DillonSimeone/ConfluenceTactoLuminateBracelet/images/datagloves/5DTDataGlove5Ultra.webp

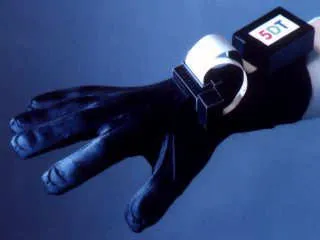
images/datagloves/5DTDataGlove5Ultra.webp
