DillonSimeone/ConfluenceTactoLuminateBracelet/images/datagloves/10FingerFlexGloves.webp

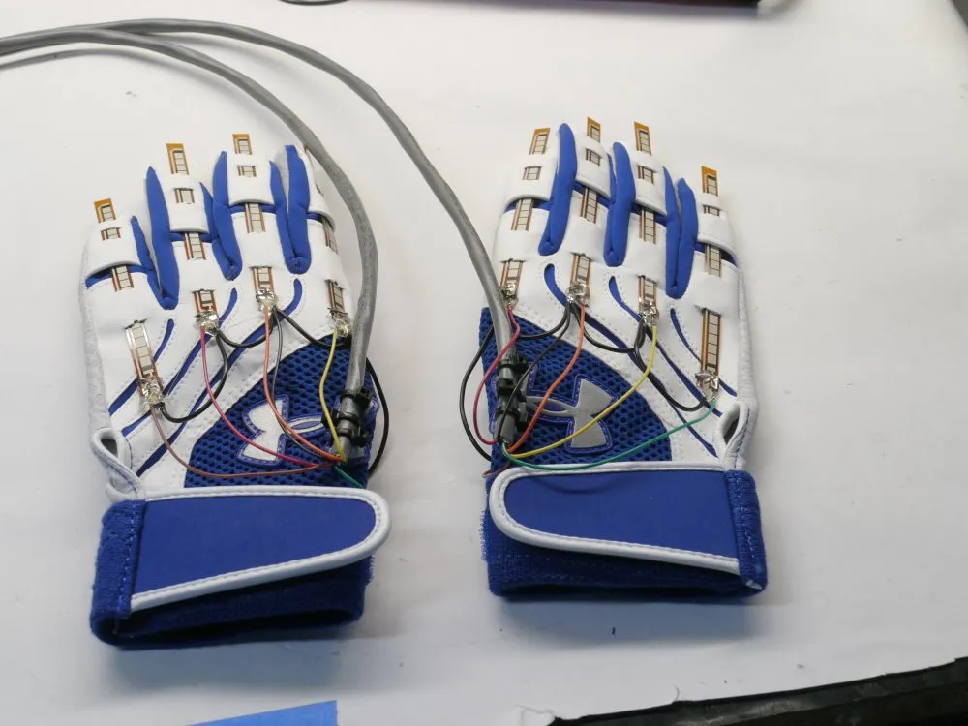
images/datagloves/10FingerFlexGloves.webp
