DillonSimeone/ConfluenceTactoLuminateBracelet/images/datagloves/acceleglove.webp

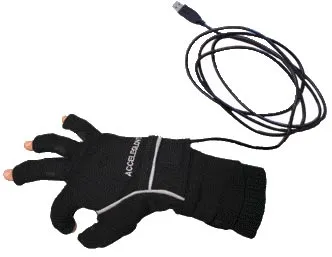
images/datagloves/acceleglove.webp
