DillonSimeone/ConfluenceTactoLuminateBracelet/images/datagloves/aura.webp

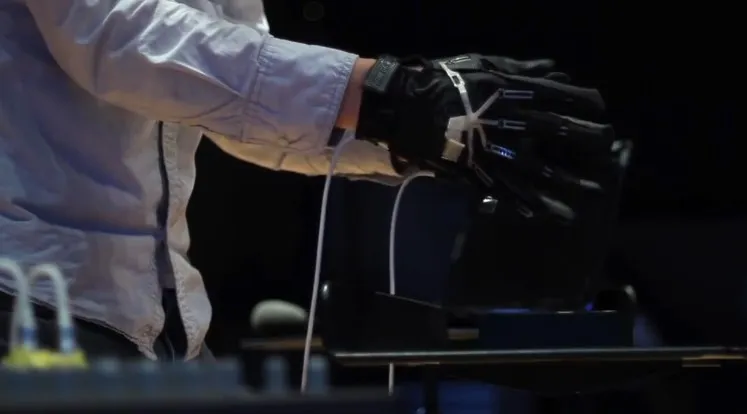
images/datagloves/aura.webp
