DillonSimeone/ConfluenceTactoLuminateBracelet/images/datagloves/CrochetGloves.webp

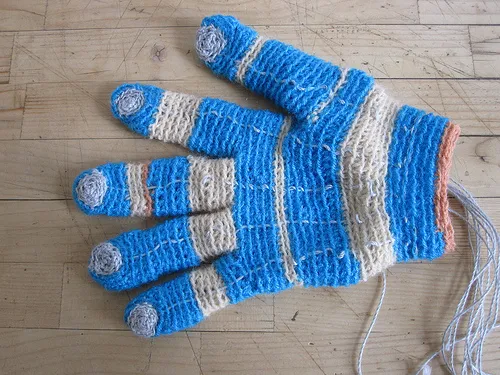
images/datagloves/CrochetGloves.webp
