DillonSimeone/ConfluenceTactoLuminateBracelet/images/datagloves/Cybergloves.webp

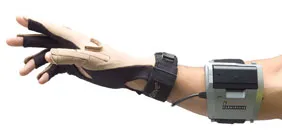
images/datagloves/Cybergloves.webp
