DillonSimeone/ConfluenceTactoLuminateBracelet/images/datagloves/Data_Glove_System.webp

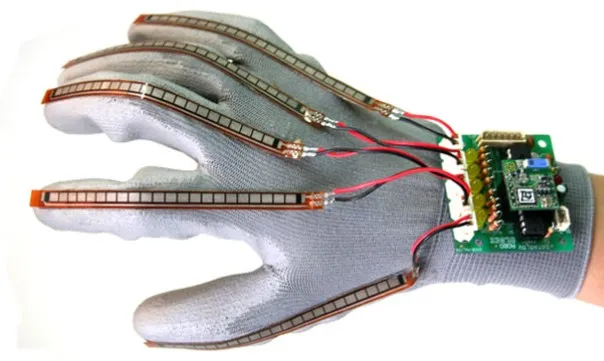
images/datagloves/Data_Glove_System.webp
