DillonSimeone/ConfluenceTactoLuminateBracelet/images/datagloves/DataGloveDarmstadt.webp

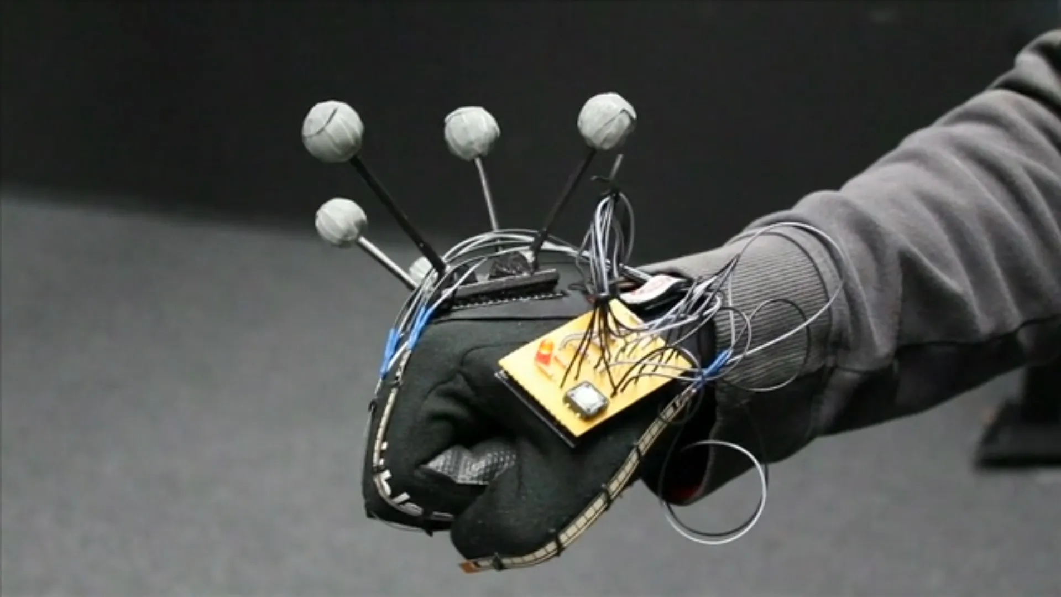
images/datagloves/DataGloveDarmstadt.webp
