DillonSimeone/ConfluenceTactoLuminateBracelet/images/datagloves/Digits.webp

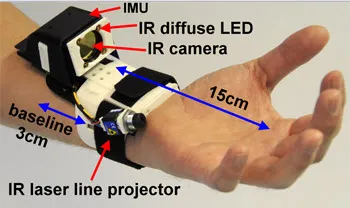
images/datagloves/Digits.webp
