DillonSimeone/ConfluenceTactoLuminateBracelet/images/datagloves/DjGLove.webp

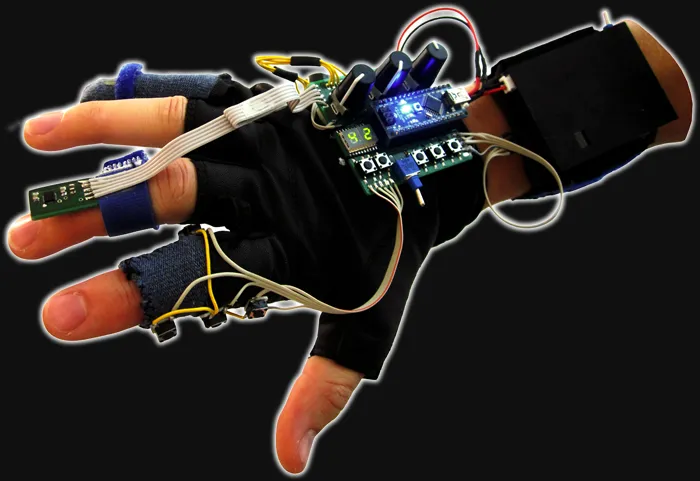
images/datagloves/DjGLove.webp
