DillonSimeone/ConfluenceTactoLuminateBracelet/images/datagloves/drawdioGlove.webp

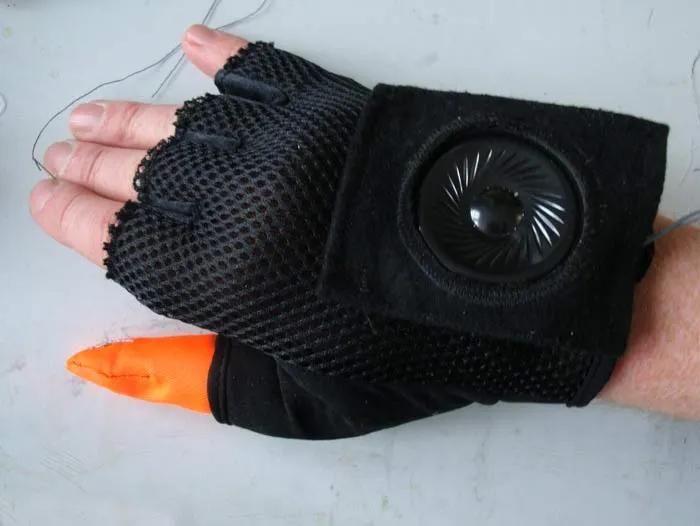
images/datagloves/drawdioGlove.webp
