DillonSimeone/ConfluenceTactoLuminateBracelet/images/datagloves/Exolux.webp

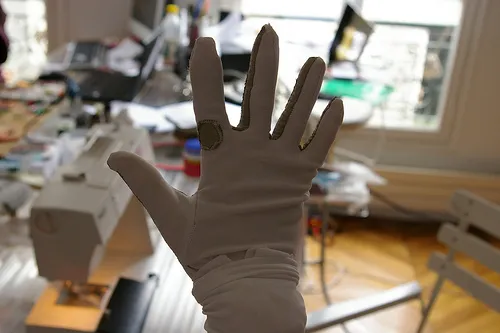
images/datagloves/Exolux.webp
