DillonSimeone/ConfluenceTactoLuminateBracelet/images/datagloves/EXOSDexterousHandMaster.webp

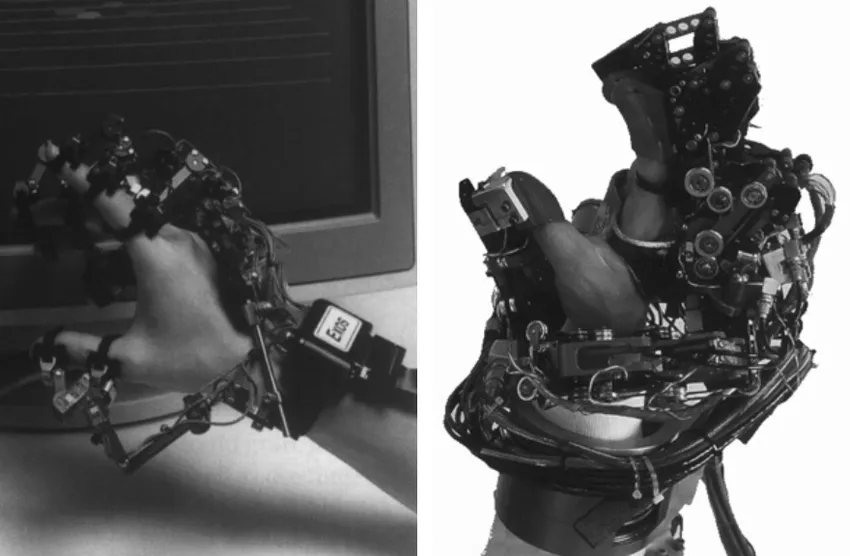
images/datagloves/EXOSDexterousHandMaster.webp
