DillonSimeone/ConfluenceTactoLuminateBracelet/images/datagloves/fingerPiano.webp

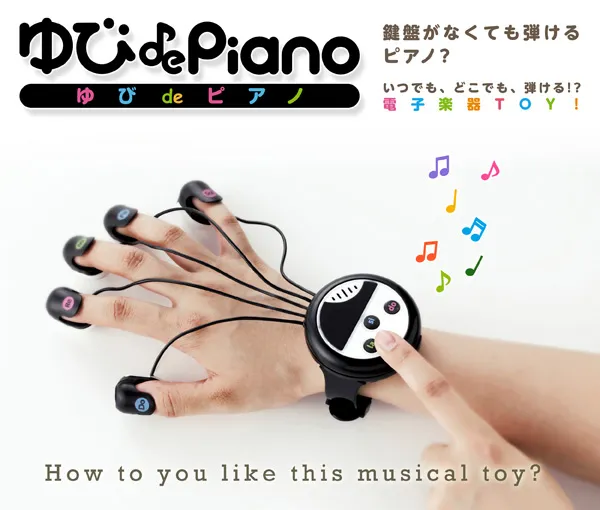
images/datagloves/fingerPiano.webp
