DillonSimeone/ConfluenceTactoLuminateBracelet/images/datagloves/FingerTPSII.webp

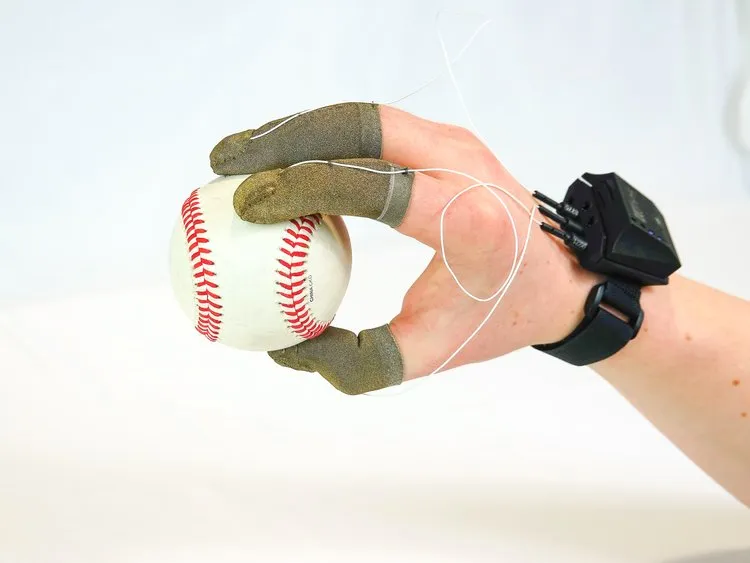
images/datagloves/FingerTPSII.webp
