DillonSimeone/ConfluenceTactoLuminateBracelet/images/datagloves/FranziskaBaumannSensorgloves.webp

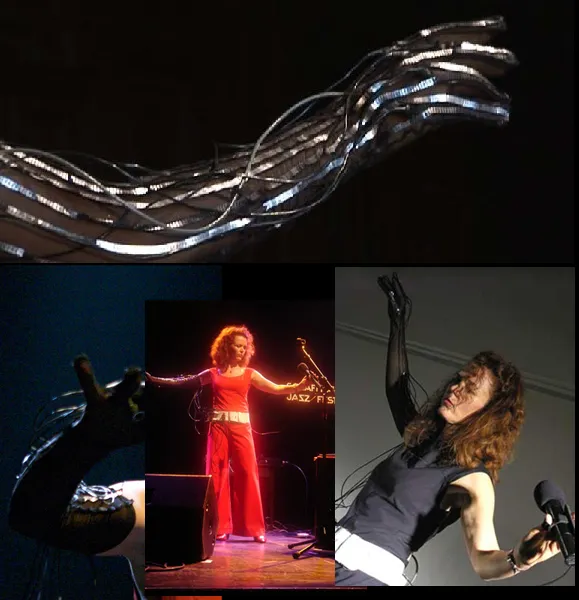
images/datagloves/FranziskaBaumannSensorgloves.webp
