DillonSimeone/ConfluenceTactoLuminateBracelet/images/datagloves/GloveOne.webp

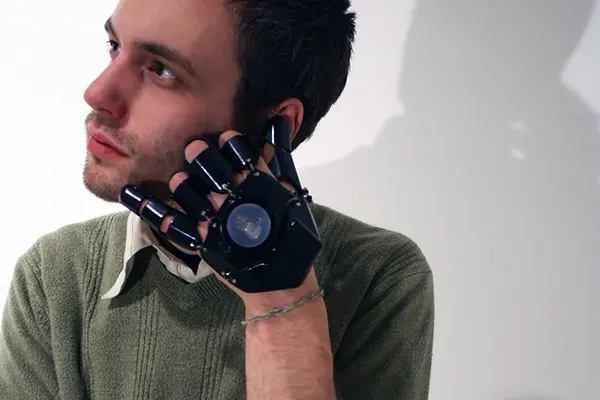
images/datagloves/GloveOne.webp
