DillonSimeone/ConfluenceTactoLuminateBracelet/images/datagloves/GlovePressureMappingSystem.webp

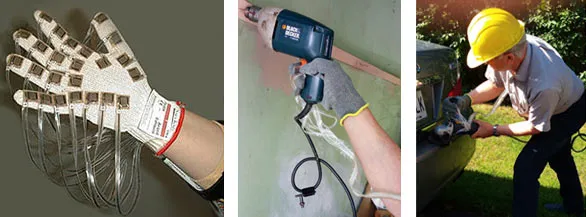
images/datagloves/GlovePressureMappingSystem.webp
