DillonSimeone/ConfluenceTactoLuminateBracelet/images/datagloves/GolanLevinHAND.webp

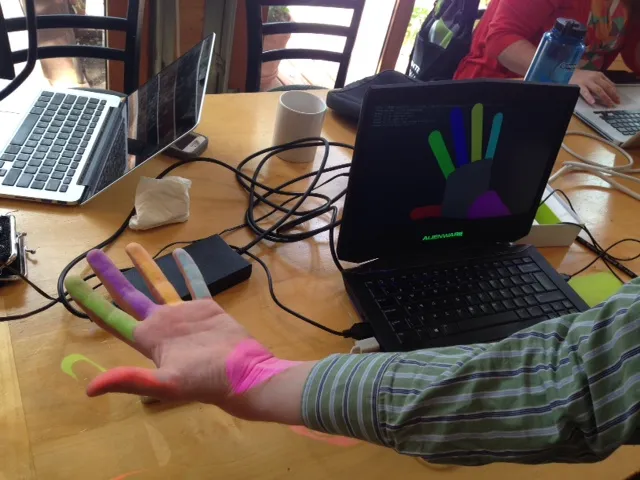
images/datagloves/GolanLevinHAND.webp
