DillonSimeone/ConfluenceTactoLuminateBracelet/images/datagloves/gStalt.webp

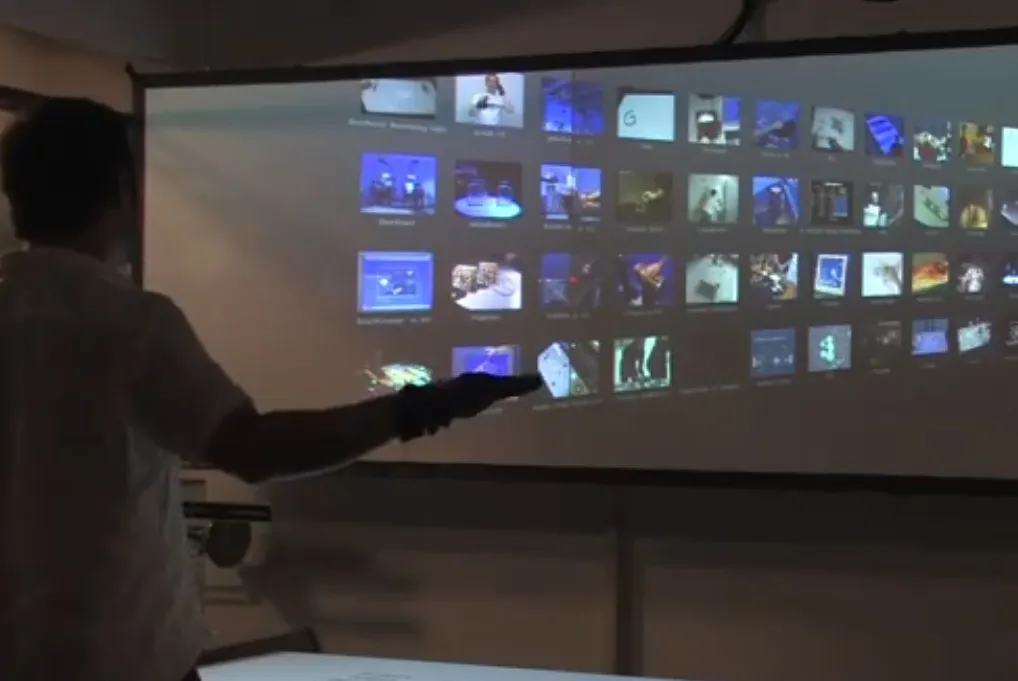
images/datagloves/gStalt.webp
