DillonSimeone/ConfluenceTactoLuminateBracelet/images/datagloves/KeyGlove.webp

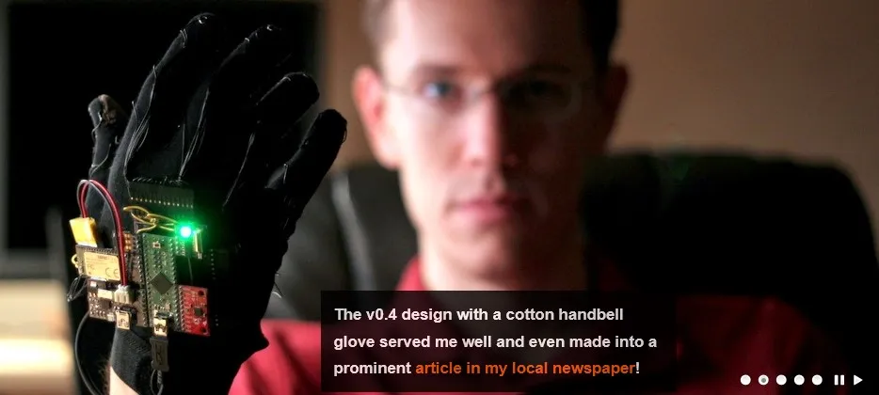
images/datagloves/KeyGlove.webp
