DillonSimeone/ConfluenceTactoLuminateBracelet/images/datagloves/ladysglove.webp

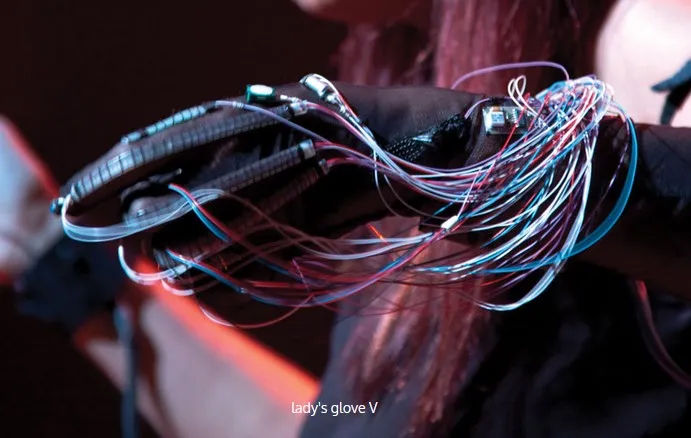
images/datagloves/ladysglove.webp
