DillonSimeone/ConfluenceTactoLuminateBracelet/images/datagloves/LuluWhite.webp

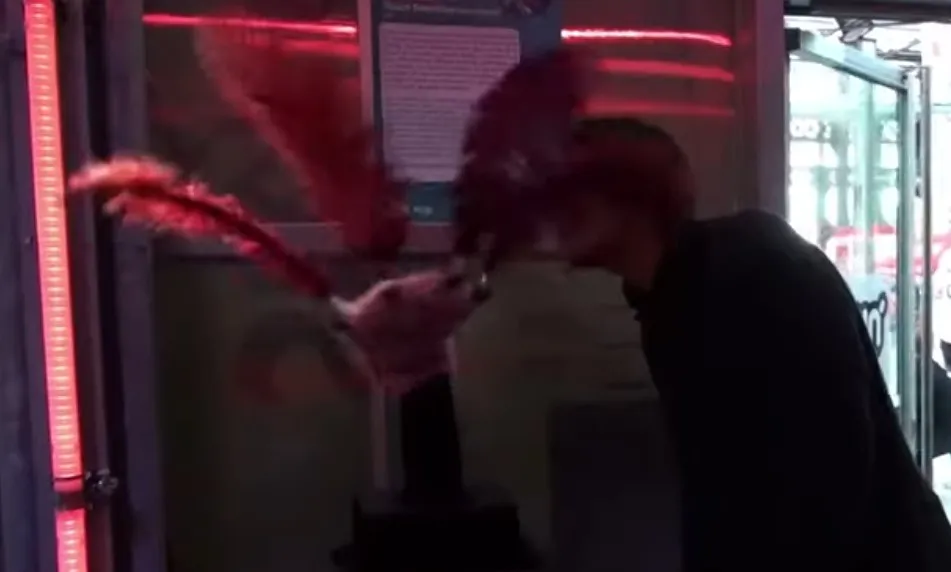
images/datagloves/LuluWhite.webp
