DillonSimeone/ConfluenceTactoLuminateBracelet/images/datagloves/Marchingbandgloves.webp

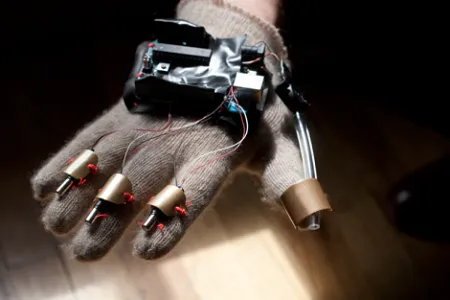
images/datagloves/Marchingbandgloves.webp
