DillonSimeone/ConfluenceTactoLuminateBracelet/images/datagloves/MediTouch-Hand-Tutor-2.webp

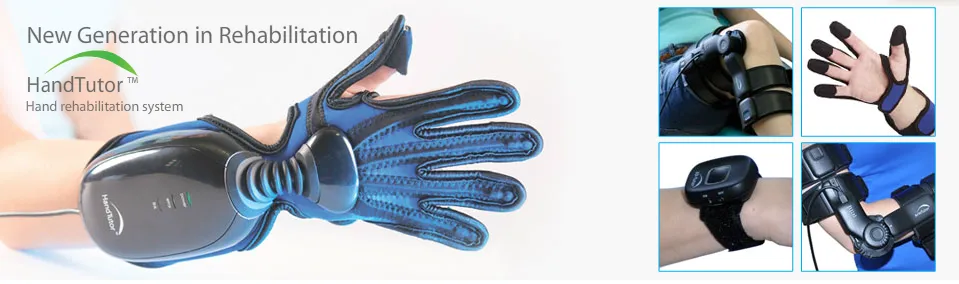
images/datagloves/MediTouch-Hand-Tutor-2.webp
