DillonSimeone/ConfluenceTactoLuminateBracelet/images/datagloves/mobile-lorm-glove-03.webp

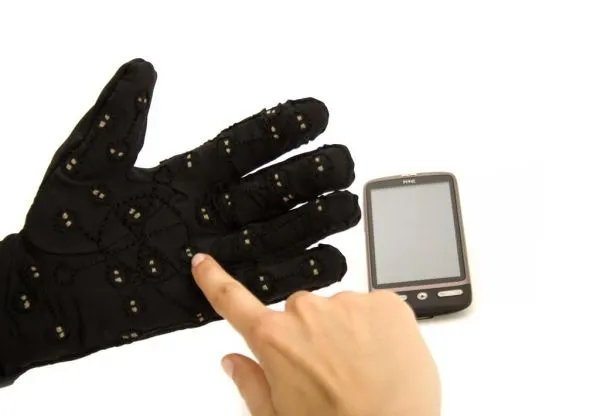
images/datagloves/mobile-lorm-glove-03.webp
