DillonSimeone/ConfluenceTactoLuminateBracelet/images/datagloves/MusicGloves.webp

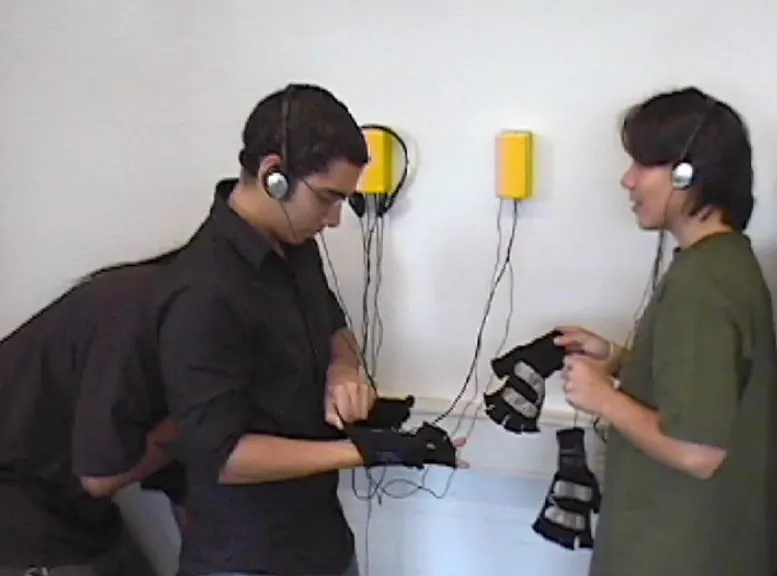
images/datagloves/MusicGloves.webp
