DillonSimeone/ConfluenceTactoLuminateBracelet/images/datagloves/peregrineglove.webp

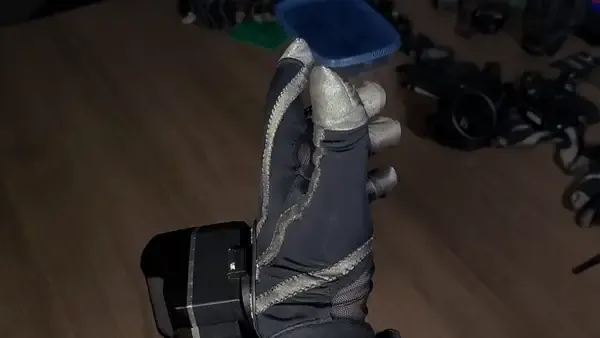
images/datagloves/peregrineglove.webp
