DillonSimeone/ConfluenceTactoLuminateBracelet/images/datagloves/PersonalInstrument.webp

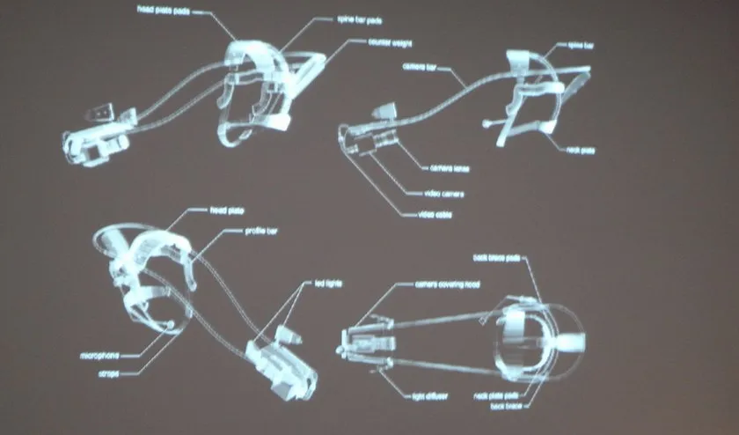
images/datagloves/PersonalInstrument.webp
