DillonSimeone/ConfluenceTactoLuminateBracelet/images/datagloves/PhaseSpaceMotionCaptureGloves.webp

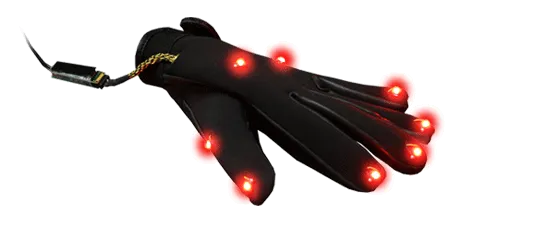
images/datagloves/PhaseSpaceMotionCaptureGloves.webp
