DillonSimeone/ConfluenceTactoLuminateBracelet/images/datagloves/PianoGloves.webp

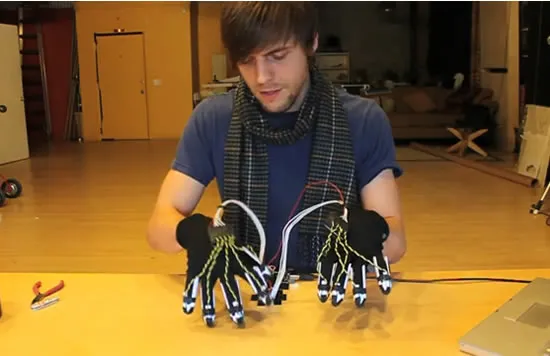
images/datagloves/PianoGloves.webp
