DillonSimeone/ConfluenceTactoLuminateBracelet/images/datagloves/pinch.webp-srcw.webp

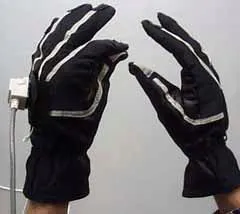
images/datagloves/pinch.webp-srcw.webp
