DillonSimeone/ConfluenceTactoLuminateBracelet/images/datagloves/plianceGloveSensor.webp

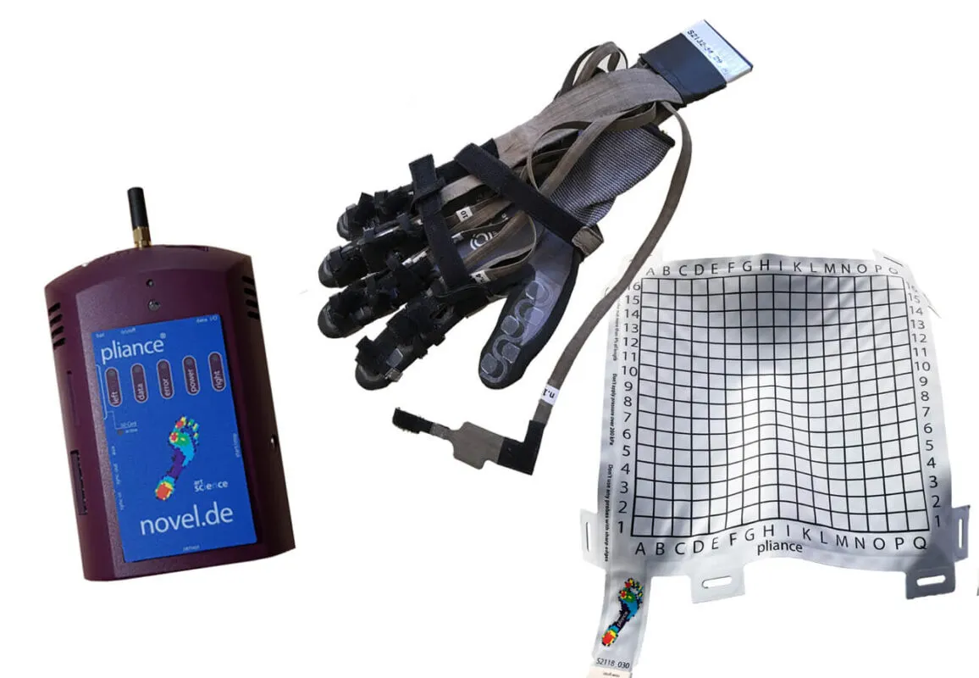
images/datagloves/plianceGloveSensor.webp
