DillonSimeone/ConfluenceTactoLuminateBracelet/images/datagloves/powerGlove.webp

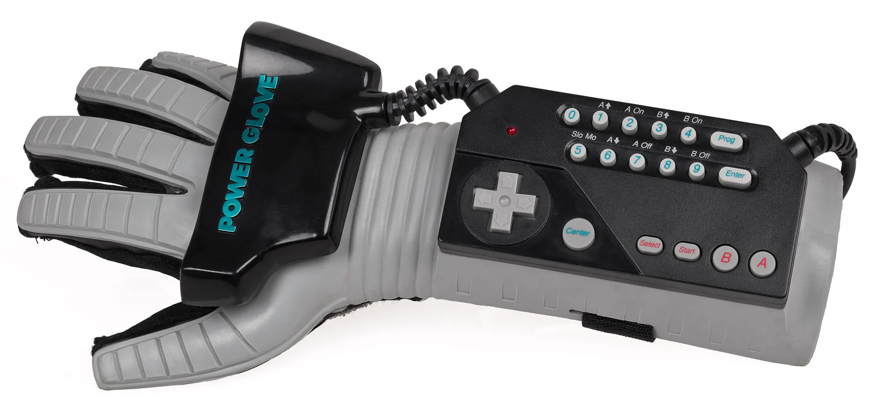
images/datagloves/powerGlove.webp
