DillonSimeone/ConfluenceTactoLuminateBracelet/images/datagloves/ProGlove.webp

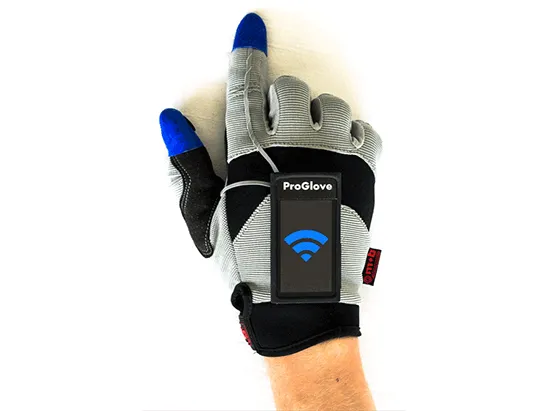
images/datagloves/ProGlove.webp
