DillonSimeone/ConfluenceTactoLuminateBracelet/images/datagloves/propinquity.webp

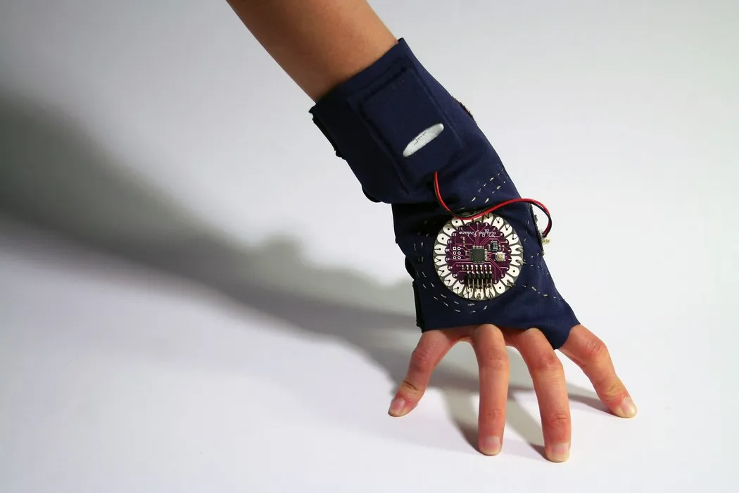
images/datagloves/propinquity.webp
