DillonSimeone/ConfluenceTactoLuminateBracelet/images/datagloves/RachelYalisoveConversationalGloves.webp

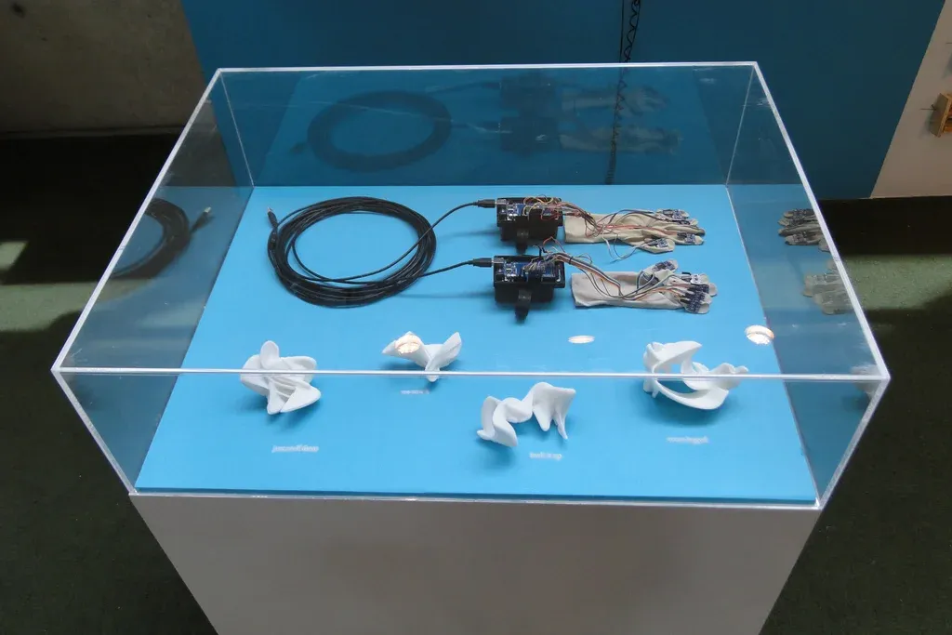
images/datagloves/RachelYalisoveConversationalGloves.webp
