DillonSimeone/ConfluenceTactoLuminateBracelet/images/datagloves/secret_keeper_72.webp

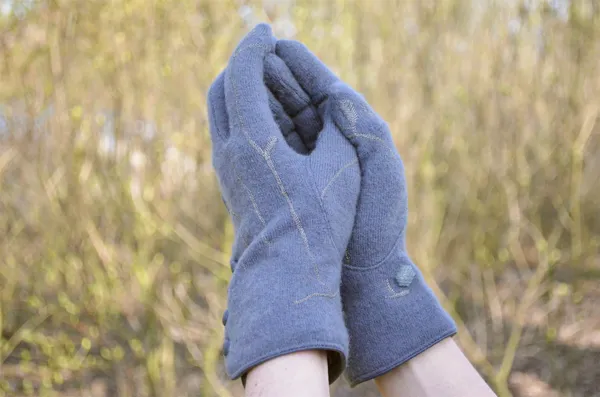
images/datagloves/secret_keeper_72.webp
