DillonSimeone/ConfluenceTactoLuminateBracelet/images/datagloves/SensitiveFingertips.webp

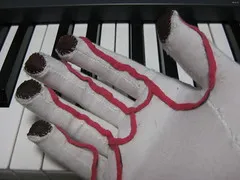
images/datagloves/SensitiveFingertips.webp
