DillonSimeone/ConfluenceTactoLuminateBracelet/images/datagloves/shakeonit.webp

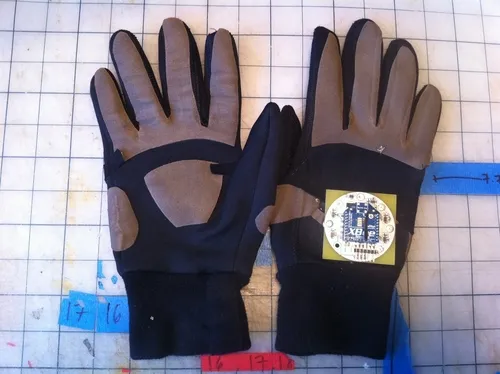
images/datagloves/shakeonit.webp
