DillonSimeone/ConfluenceTactoLuminateBracelet/images/datagloves/Signlanguagetranslation.webp

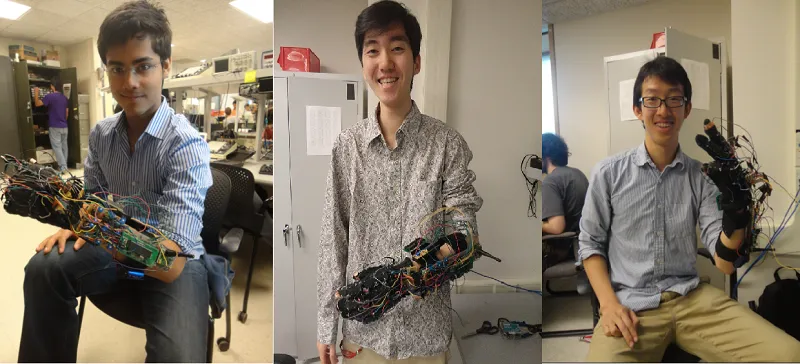
images/datagloves/Signlanguagetranslation.webp
