DillonSimeone/ConfluenceTactoLuminateBracelet/images/datagloves/sneakyGestures.webp

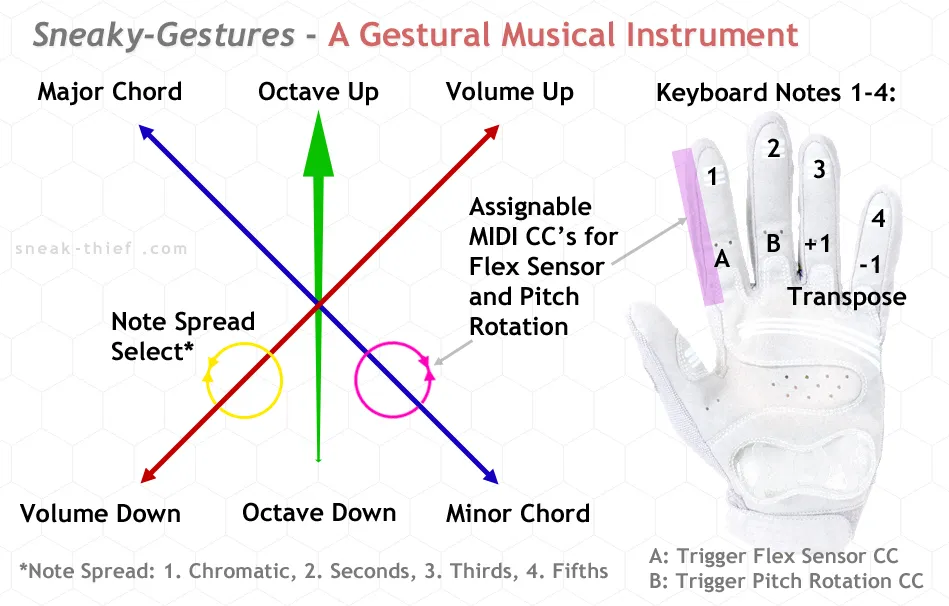
images/datagloves/sneakyGestures.webp
