DillonSimeone/ConfluenceTactoLuminateBracelet/images/datagloves/stretchSense.webp

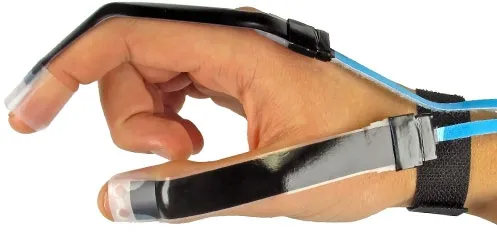
images/datagloves/stretchSense.webp
