DillonSimeone/ConfluenceTactoLuminateBracelet/images/datagloves/T(ether).webp

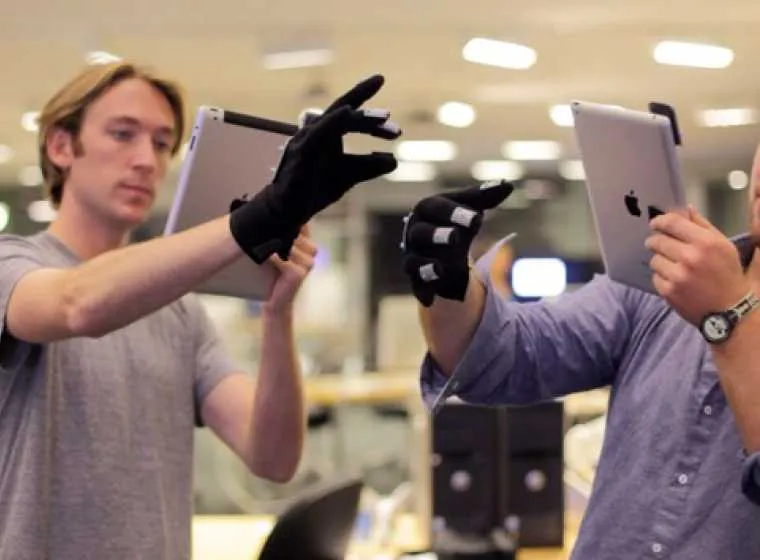
images/datagloves/T(ether).webp
