DillonSimeone/ConfluenceTactoLuminateBracelet/images/datagloves/TacitLanguage.webp

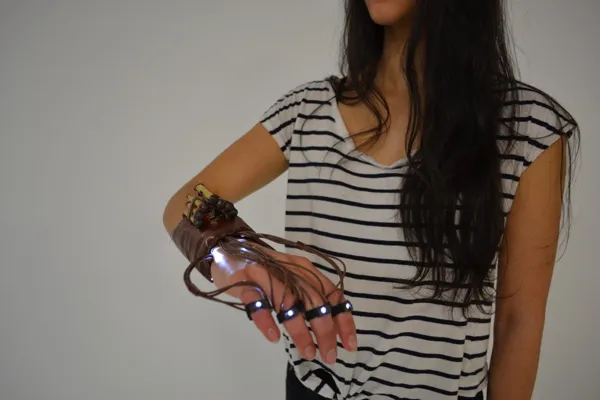
images/datagloves/TacitLanguage.webp
