DillonSimeone/ConfluenceTactoLuminateBracelet/images/datagloves/The-Image-Based-Data-Glove-proto-type-a-camera-attached-to-the-users-hand-tracks.webp

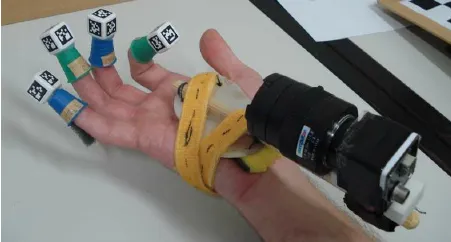
images/datagloves/The-Image-Based-Data-Glove-proto-type-a-camera-attached-to-the-users-hand-tracks.webp
