DillonSimeone/ConfluenceTactoLuminateBracelet/images/datagloves/TheVPLDataGlove.webp

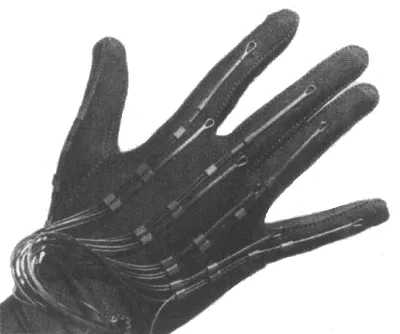
images/datagloves/TheVPLDataGlove.webp
