DillonSimeone/ConfluenceTactoLuminateBracelet/images/datagloves/TouchGlove2.webp

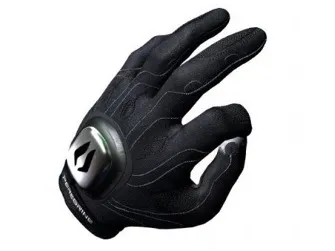
images/datagloves/TouchGlove2.webp
