DillonSimeone/ConfluenceTactoLuminateBracelet/images/datagloves/TradeMarkG.webp

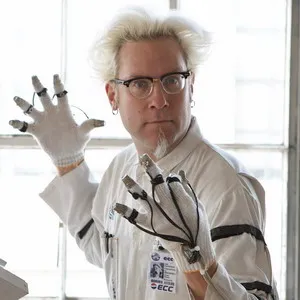
images/datagloves/TradeMarkG.webp
