DillonSimeone/ConfluenceTactoLuminateBracelet/images/datagloves/udun.webp

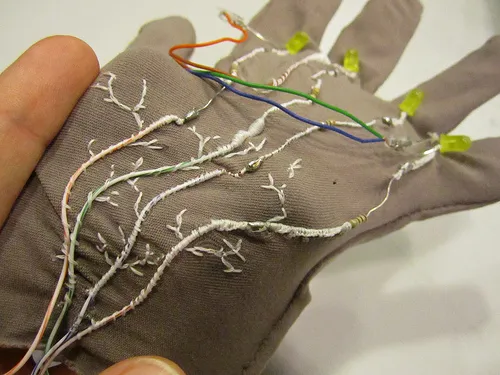
images/datagloves/udun.webp
