DillonSimeone/ConfluenceTactoLuminateBracelet/images/datagloves/vamp.webp

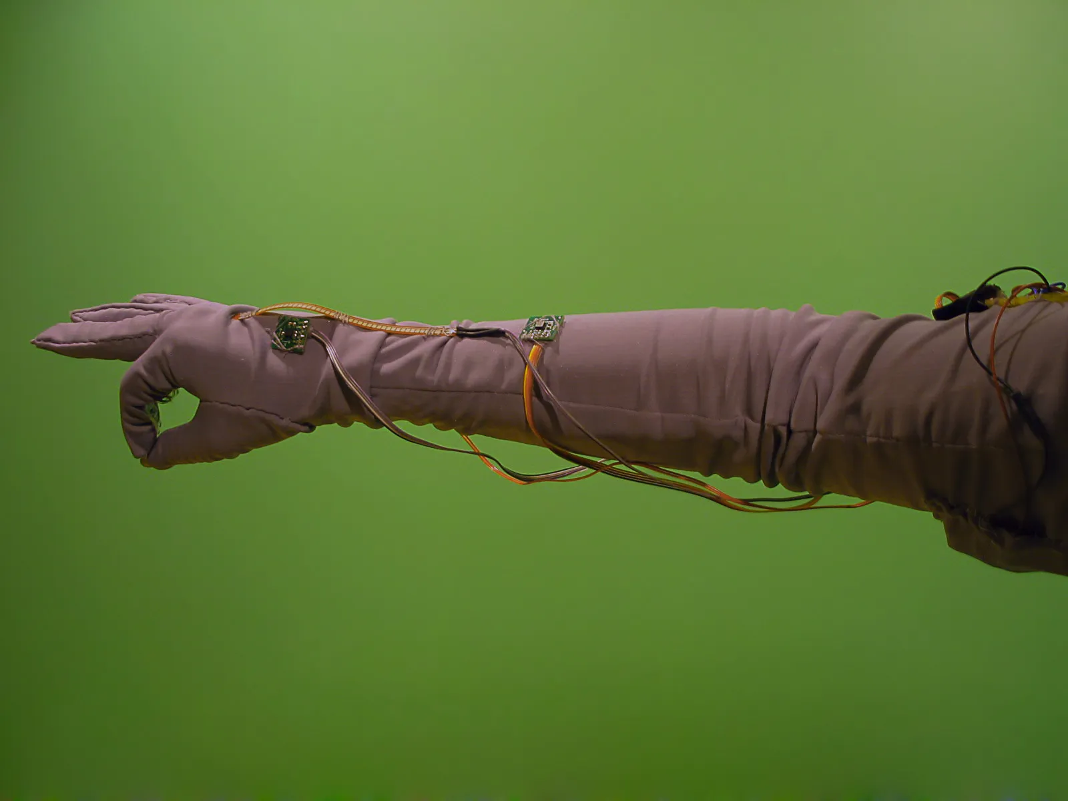
images/datagloves/vamp.webp
