DillonSimeone/ConfluenceTactoLuminateBracelet/images/datagloves/wristflicker.webp

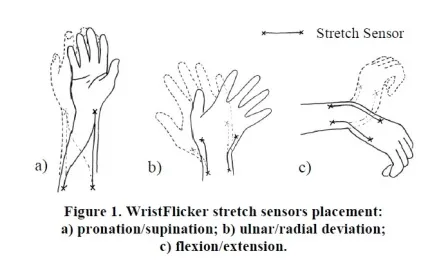
images/datagloves/wristflicker.webp
