DillonSimeone/ConfluenceTactoLuminateBracelet/images/datagloves/YouRehab.webp

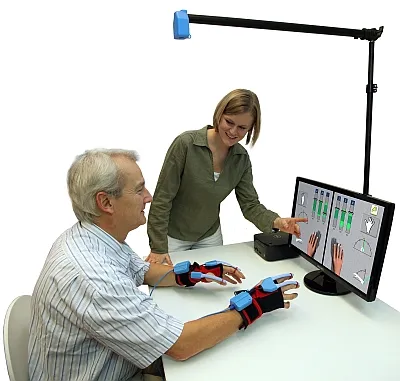
images/datagloves/YouRehab.webp
