DillonSimeone/ConfluenceTactoLuminateBracelet/images/eventsNews/capStone.jpg

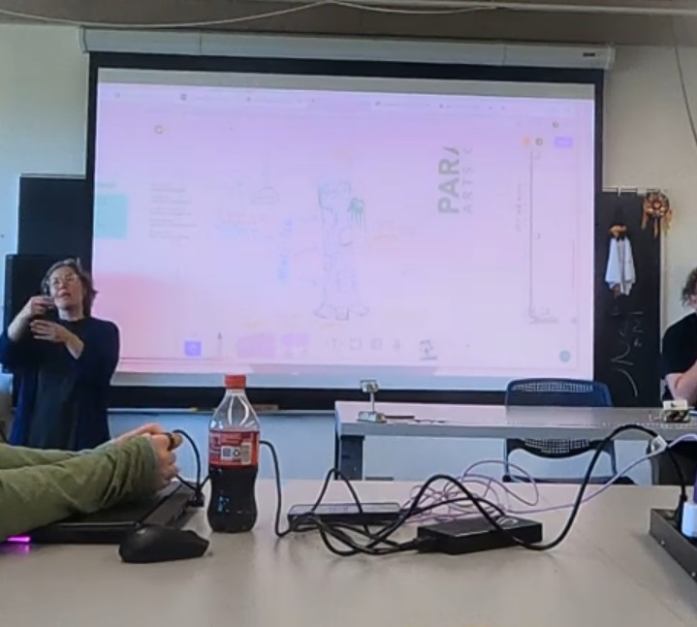
images/eventsNews/capStone.jpg
