DillonSimeone/ConfluenceTactoLuminateBracelet/images/eventsNews/CentralStateofMind.jpg

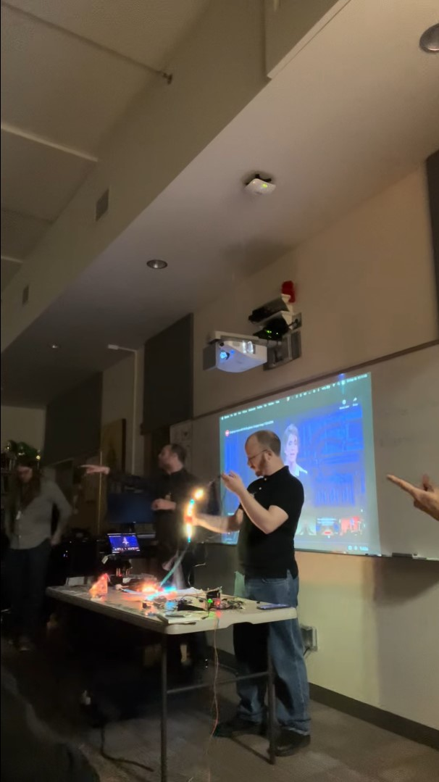
images/eventsNews/CentralStateofMind.jpg
