DillonSimeone/ConfluenceTactoLuminateBracelet/images/eventsNews/chruchWorkshop.jpg

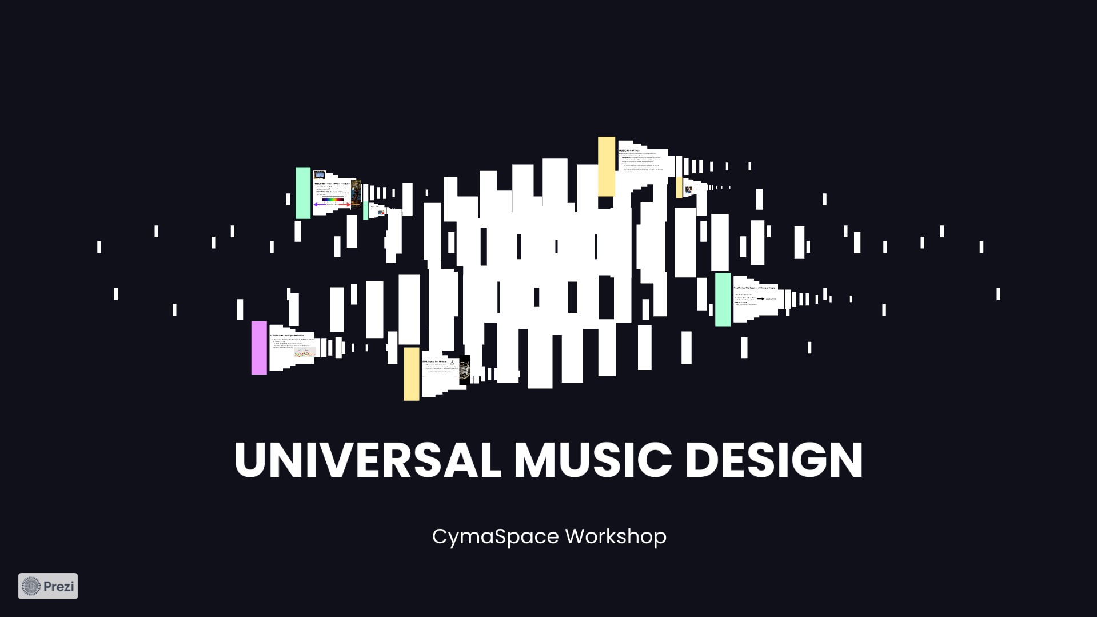
images/eventsNews/chruchWorkshop.jpg
