DillonSimeone/ConfluenceTactoLuminateBracelet/images/eventsNews/deafCafeAIImage.png

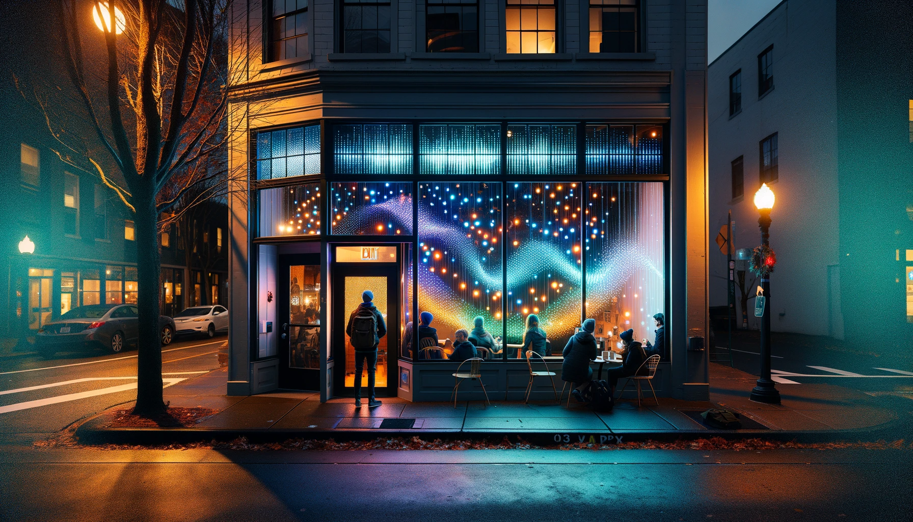
images/eventsNews/deafCafeAIImage.png
