DillonSimeone/ConfluenceTactoLuminateBracelet/images/eventsNews/hapticzoo1.jpg

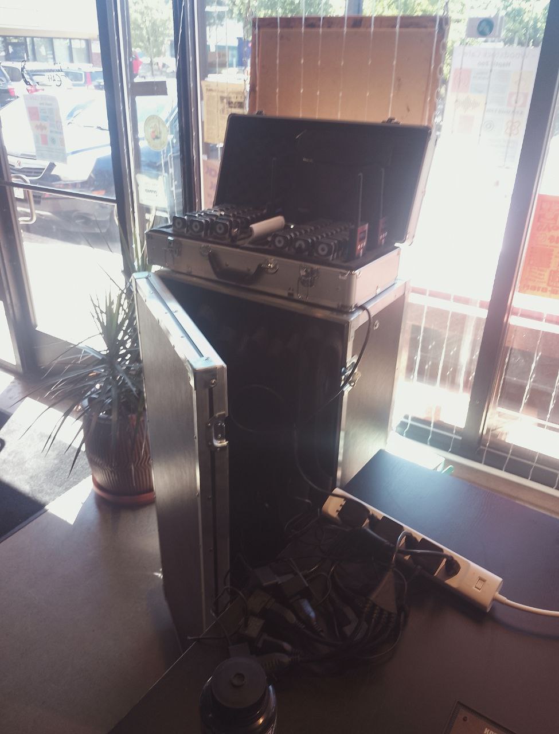
images/eventsNews/hapticzoo1.jpg
