DillonSimeone/ConfluenceTactoLuminateBracelet/images/eventsNews/hapticzoo2.jpg

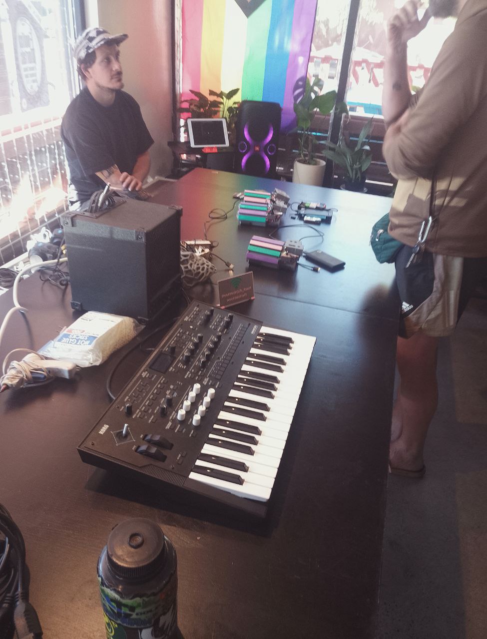
images/eventsNews/hapticzoo2.jpg
