DillonSimeone/ConfluenceTactoLuminateBracelet/images/eventsNews/hapticzoo3.jpg

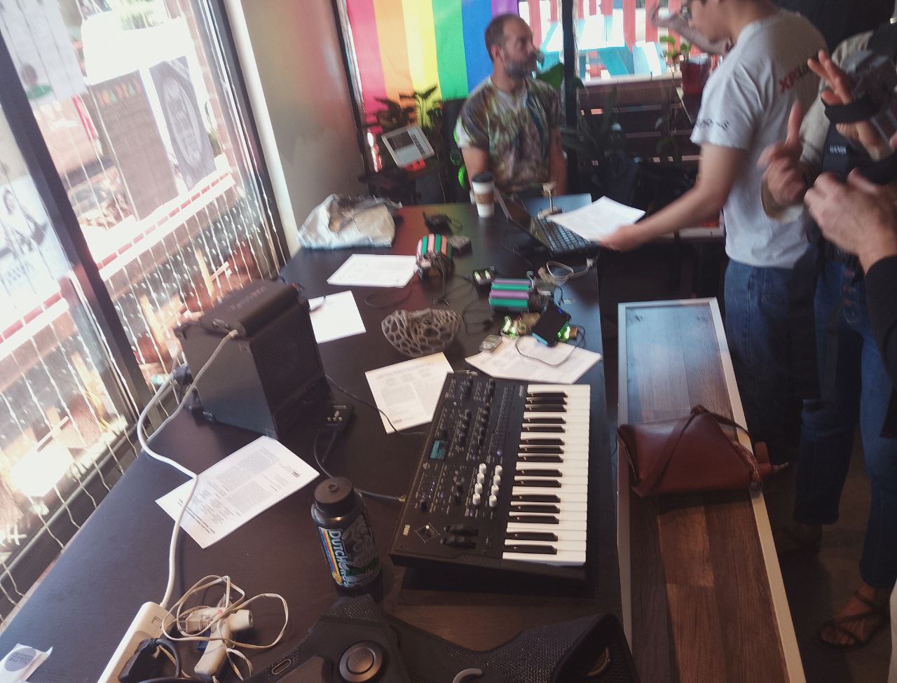
images/eventsNews/hapticzoo3.jpg
