DillonSimeone/ConfluenceTactoLuminateBracelet/images/eventsNews/hapticzoo4.jpg

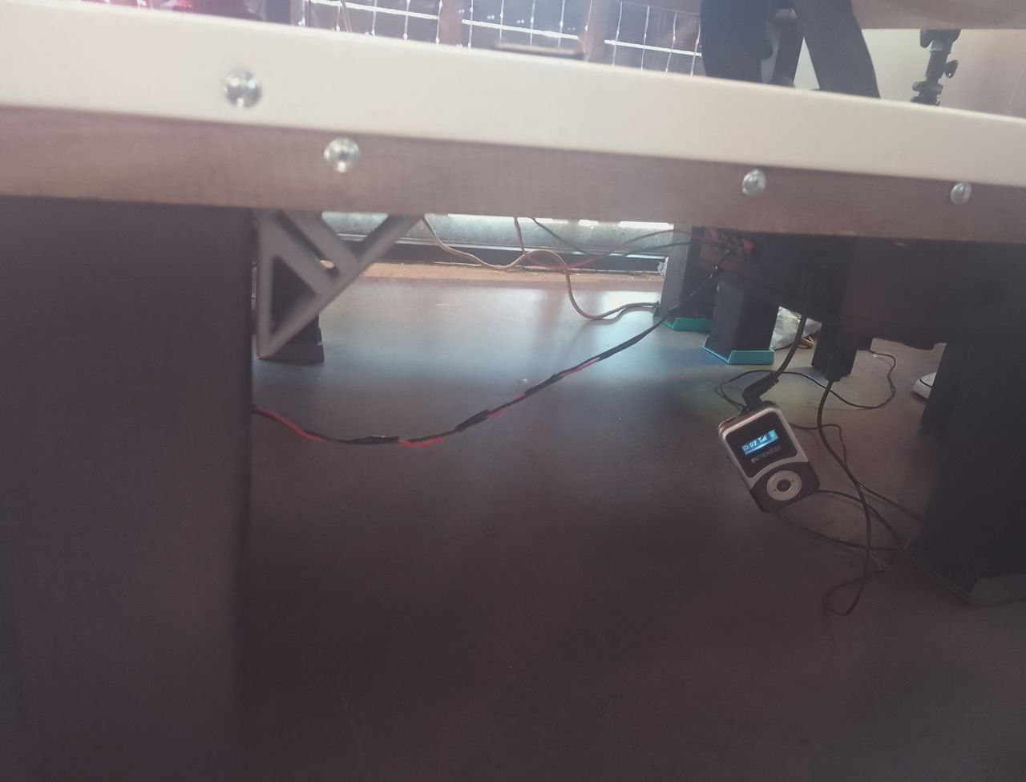
images/eventsNews/hapticzoo4.jpg
