DillonSimeone/ConfluenceTactoLuminateBracelet/images/eventsNews/hapticzoo5.jpg

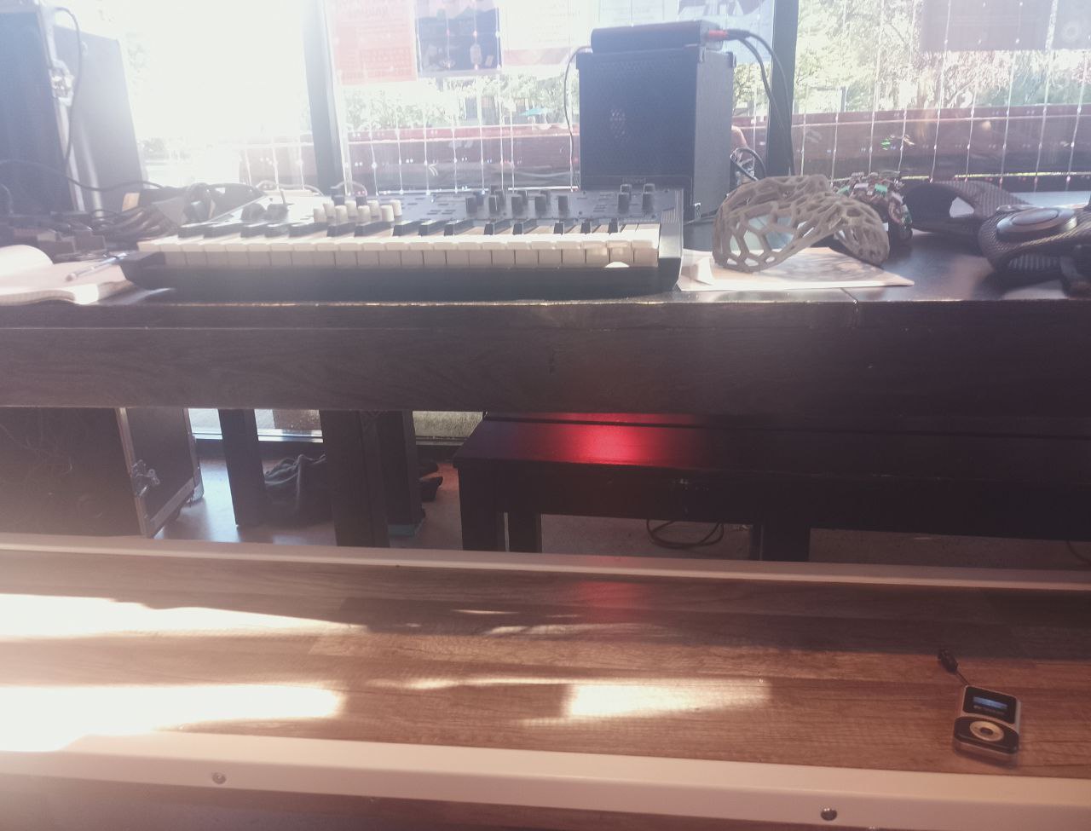
images/eventsNews/hapticzoo5.jpg
