DillonSimeone/ConfluenceTactoLuminateBracelet/images/eventsNews/hapticZoo.png

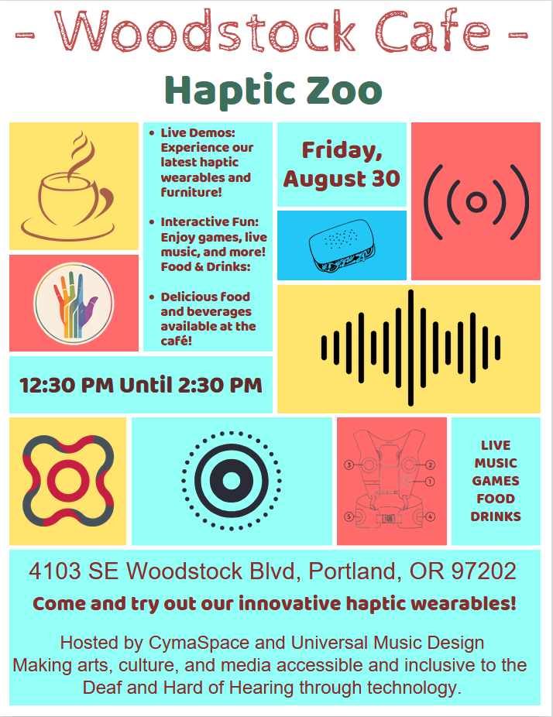
images/eventsNews/hapticZoo.png
