DillonSimeone/ConfluenceTactoLuminateBracelet/images/eventsNews/jazzRoadswebp.webp

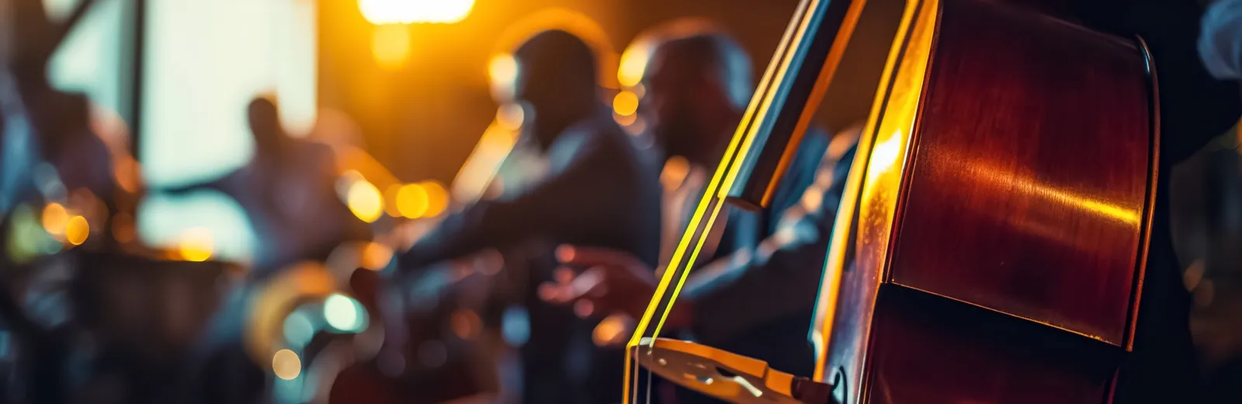
images/eventsNews/jazzRoadswebp.webp
