DillonSimeone/ConfluenceTactoLuminateBracelet/images/eventsNews/musicsonicarts.jpg

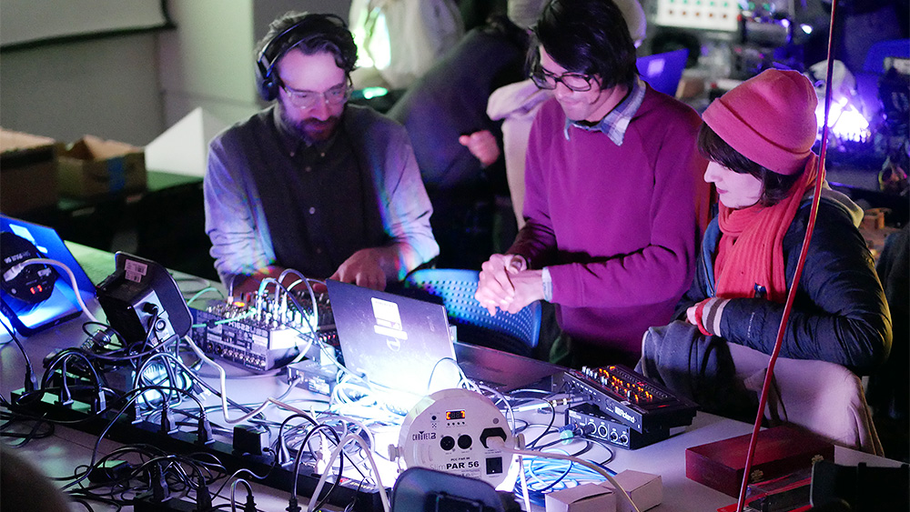
images/eventsNews/musicsonicarts.jpg
