DillonSimeone/ConfluenceTactoLuminateBracelet/images/eventsNews/NIME2024.jpg

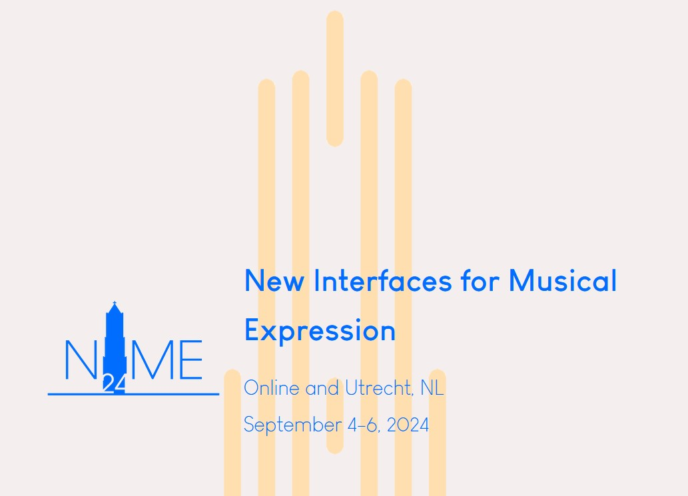
images/eventsNews/NIME2024.jpg
