DillonSimeone/ConfluenceTactoLuminateBracelet/images/eventsNews/NOTIMPOSSIBLE.jpg

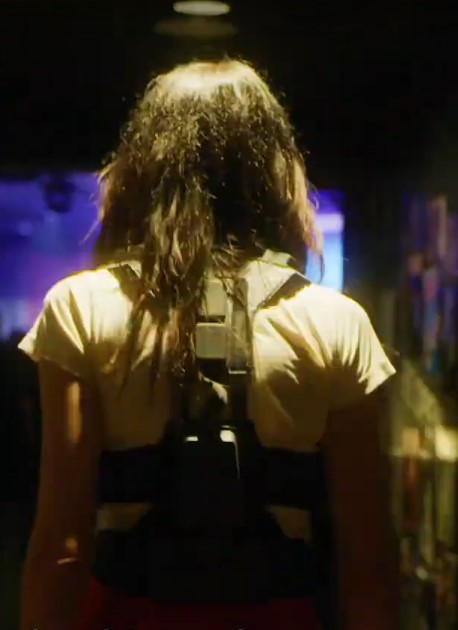
images/eventsNews/NOTIMPOSSIBLE.jpg
