DillonSimeone/ConfluenceTactoLuminateBracelet/images/eventsNews/OFCInvests1Million.jpg

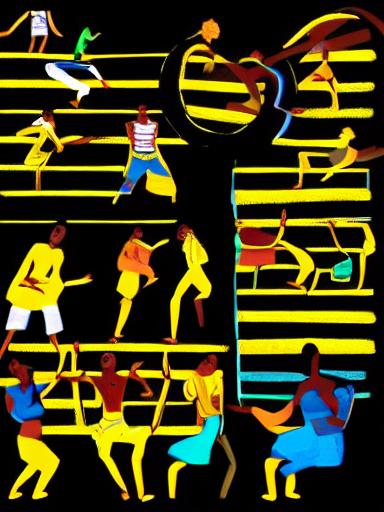
images/eventsNews/OFCInvests1Million.jpg
