DillonSimeone/ConfluenceTactoLuminateBracelet/images/eventsNews/osd1.jpg

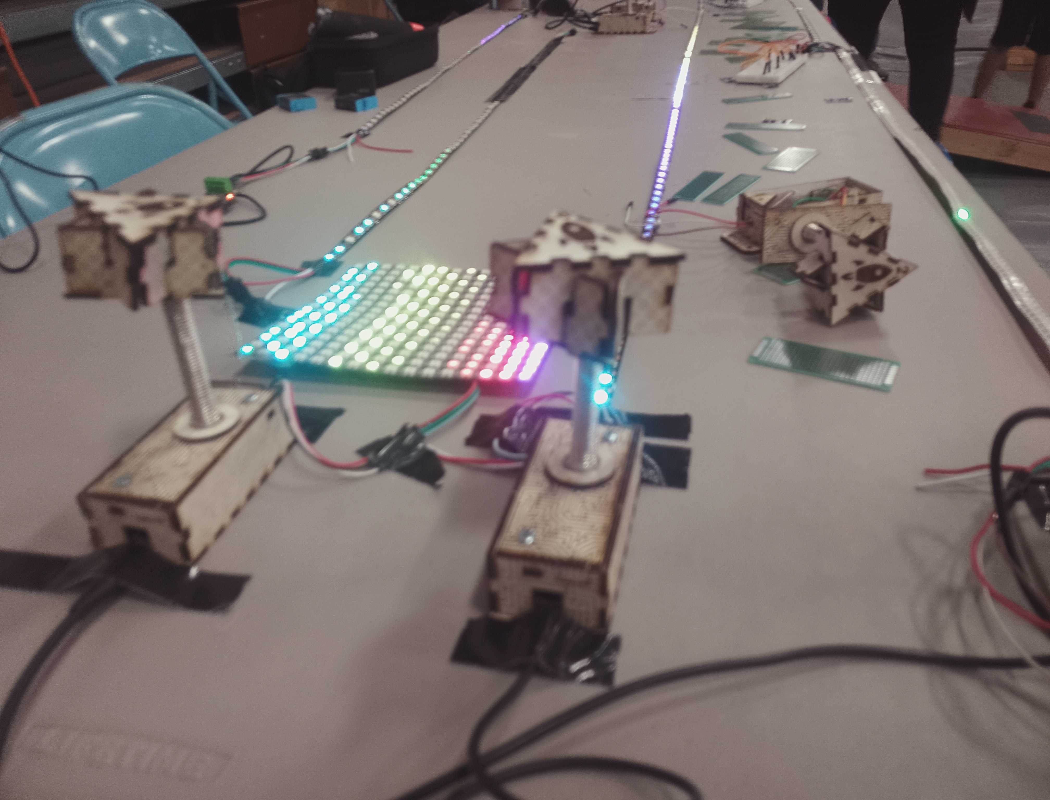
images/eventsNews/osd1.jpg
