DillonSimeone/ConfluenceTactoLuminateBracelet/images/eventsNews/osd2.jpg

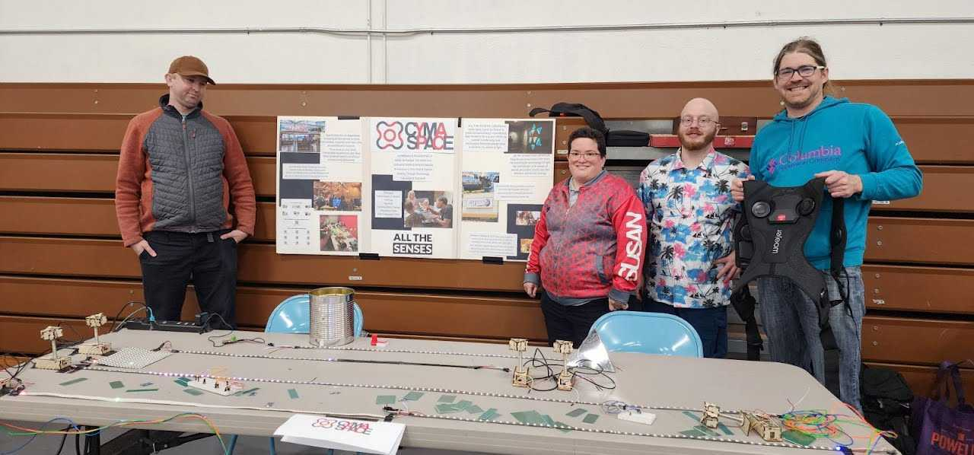
images/eventsNews/osd2.jpg
