DillonSimeone/ConfluenceTactoLuminateBracelet/images/eventsNews/osd3.jpg

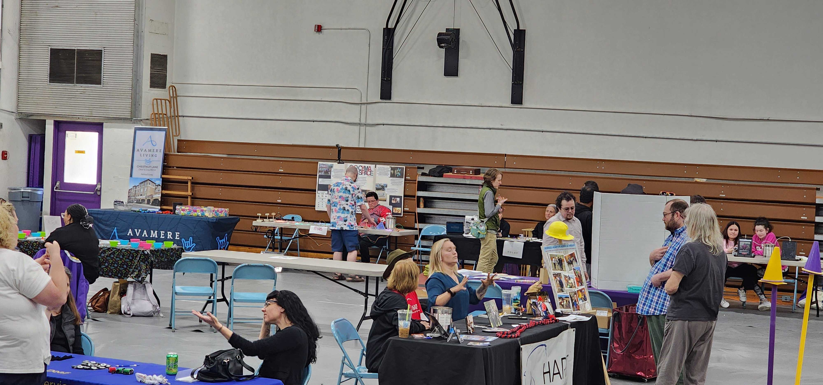
images/eventsNews/osd3.jpg
