DillonSimeone/ConfluenceTactoLuminateBracelet/images/eventsNews/osd4.jpg

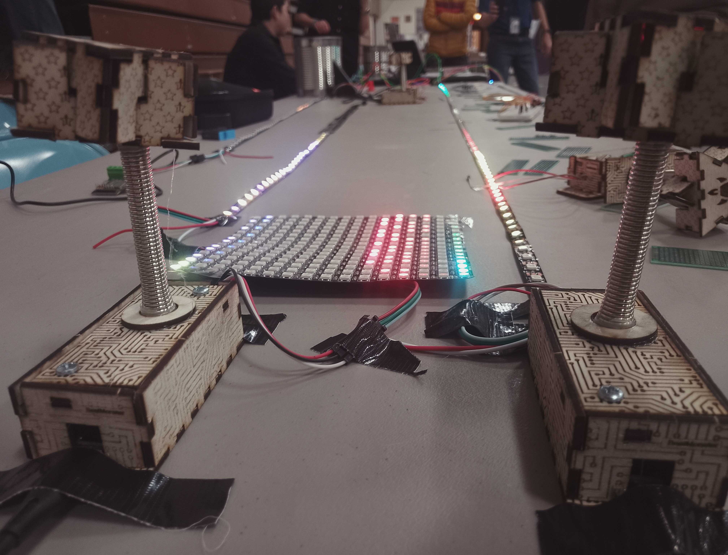
images/eventsNews/osd4.jpg
