DillonSimeone/ConfluenceTactoLuminateBracelet/images/eventsNews/osd5.jpg

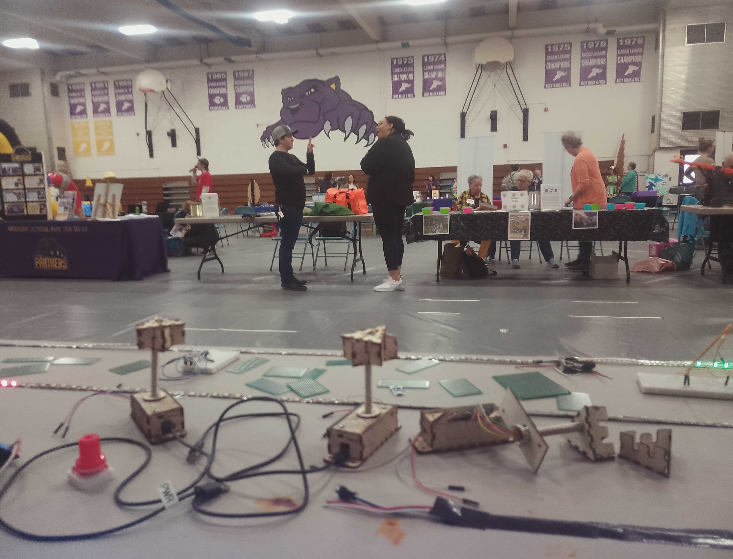
images/eventsNews/osd5.jpg
