DillonSimeone/ConfluenceTactoLuminateBracelet/images/eventsNews/RACCgrant.jpg

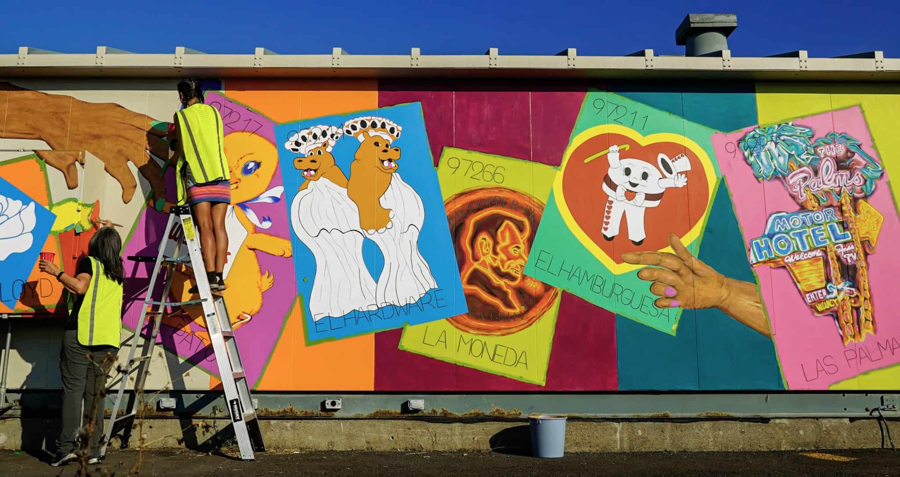
images/eventsNews/RACCgrant.jpg
