DillonSimeone/ConfluenceTactoLuminateBracelet/images/eventsNews/RainbowPrism.jpg

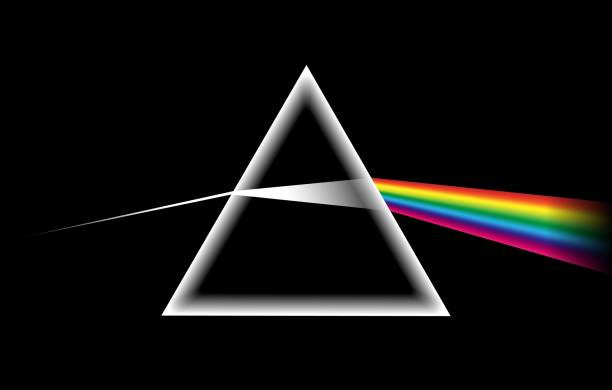
images/eventsNews/RainbowPrism.jpg
