DillonSimeone/ConfluenceTactoLuminateBracelet/images/eventsNews/ShawnandNate.jpg

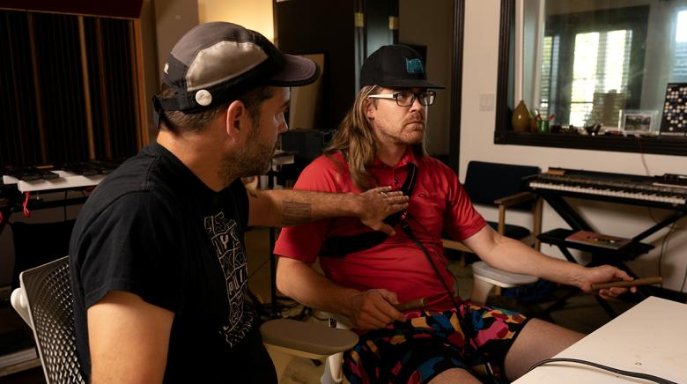
images/eventsNews/ShawnandNate.jpg
