DillonSimeone/ConfluenceTactoLuminateBracelet/images/eventsNews/studioPicture.jpg

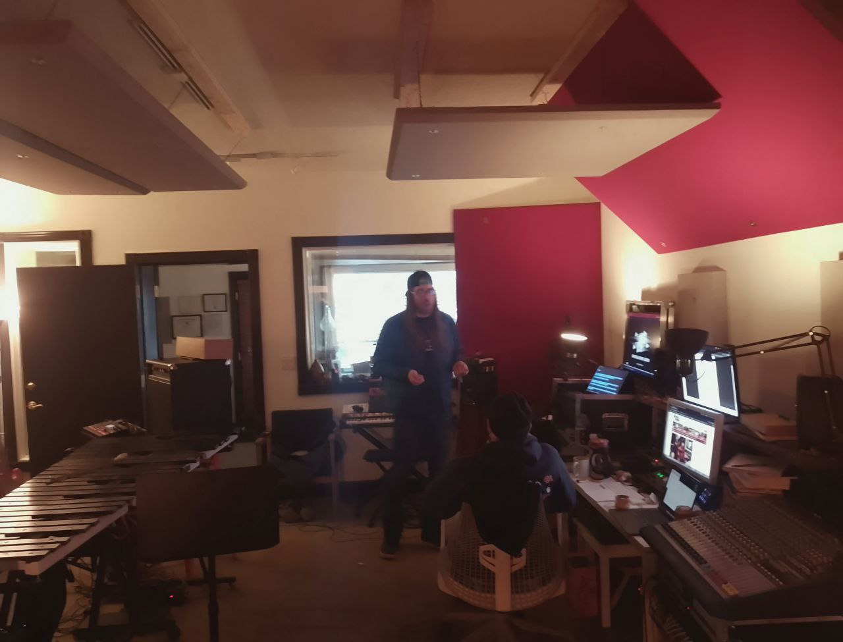
images/eventsNews/studioPicture.jpg
