DillonSimeone/ConfluenceTactoLuminateBracelet/images/eventsNews/tamcoma.jpg

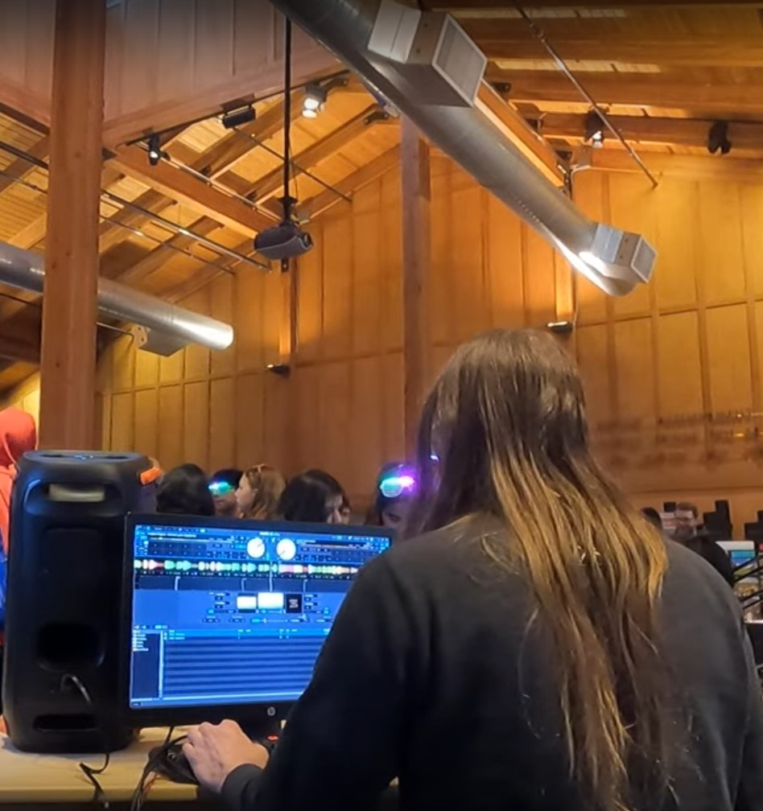
images/eventsNews/tamcoma.jpg
