DillonSimeone/ConfluenceTactoLuminateBracelet/images/eventsNews/thethirdthing1.jpg

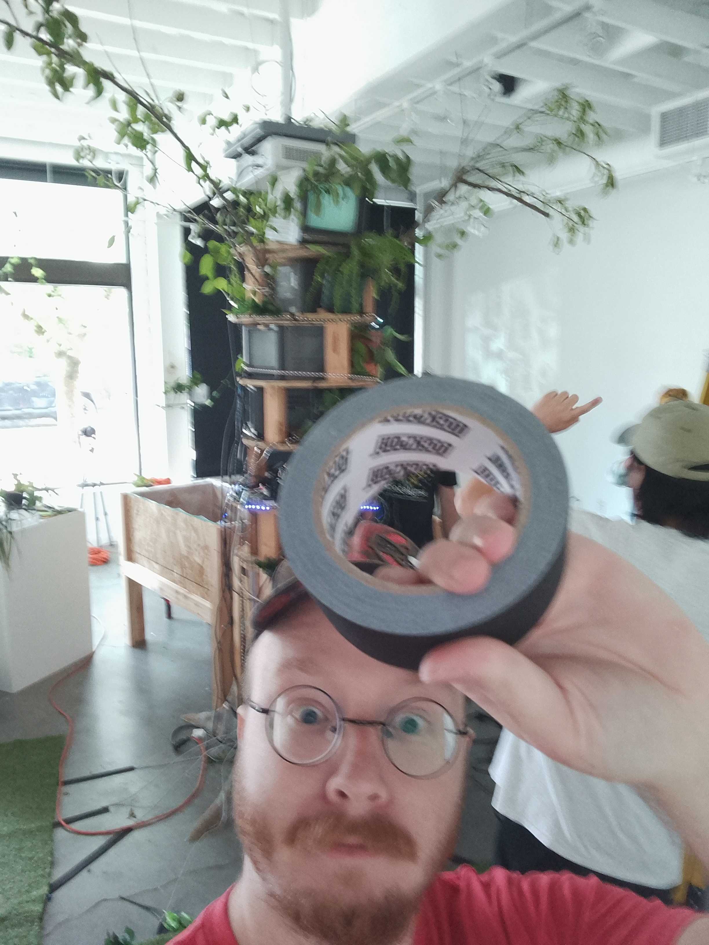
images/eventsNews/thethirdthing1.jpg
