DillonSimeone/ConfluenceTactoLuminateBracelet/images/eventsNews/thethirdthing2.jpg

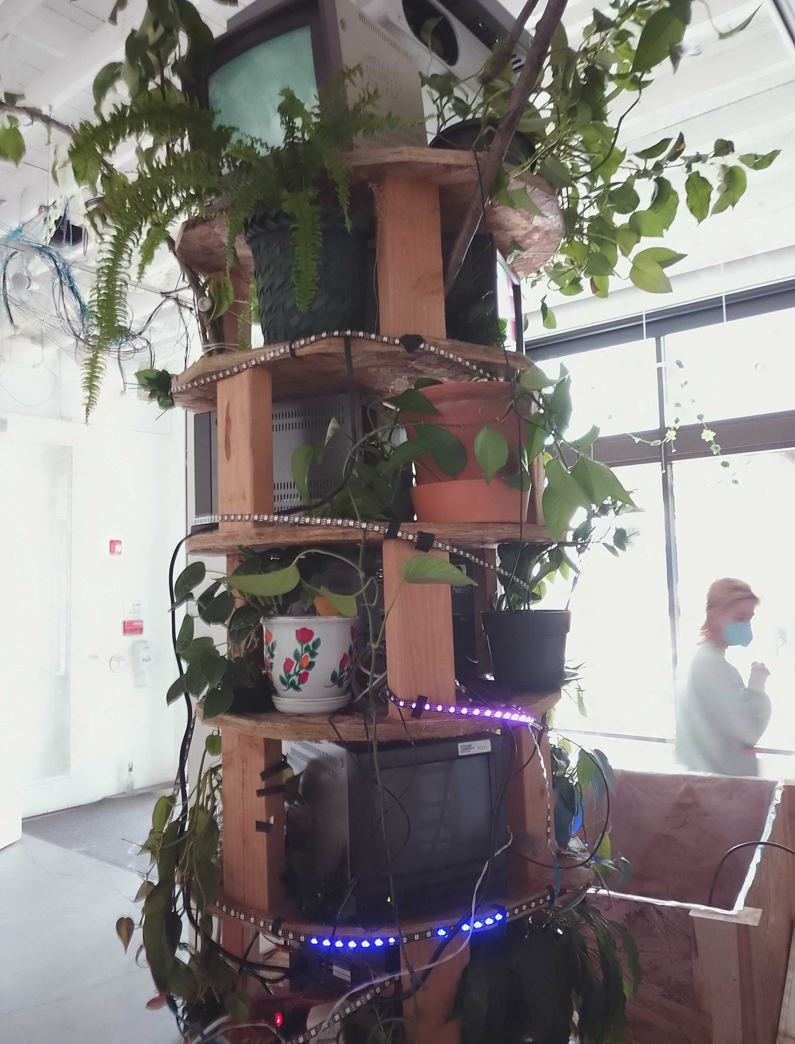
images/eventsNews/thethirdthing2.jpg
