DillonSimeone/ConfluenceTactoLuminateBracelet/images/eventsNews/thethirdthing3.jpg

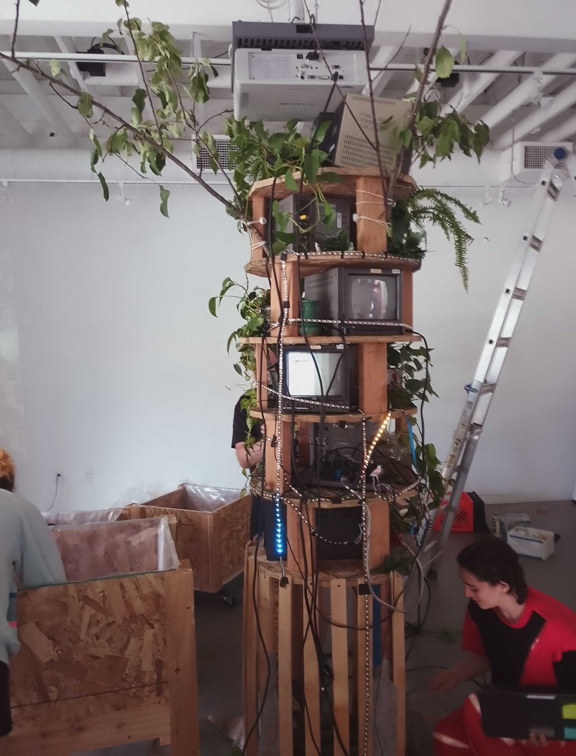
images/eventsNews/thethirdthing3.jpg
