DillonSimeone/ConfluenceTactoLuminateBracelet/images/eventsNews/thethirdthing4.jpg

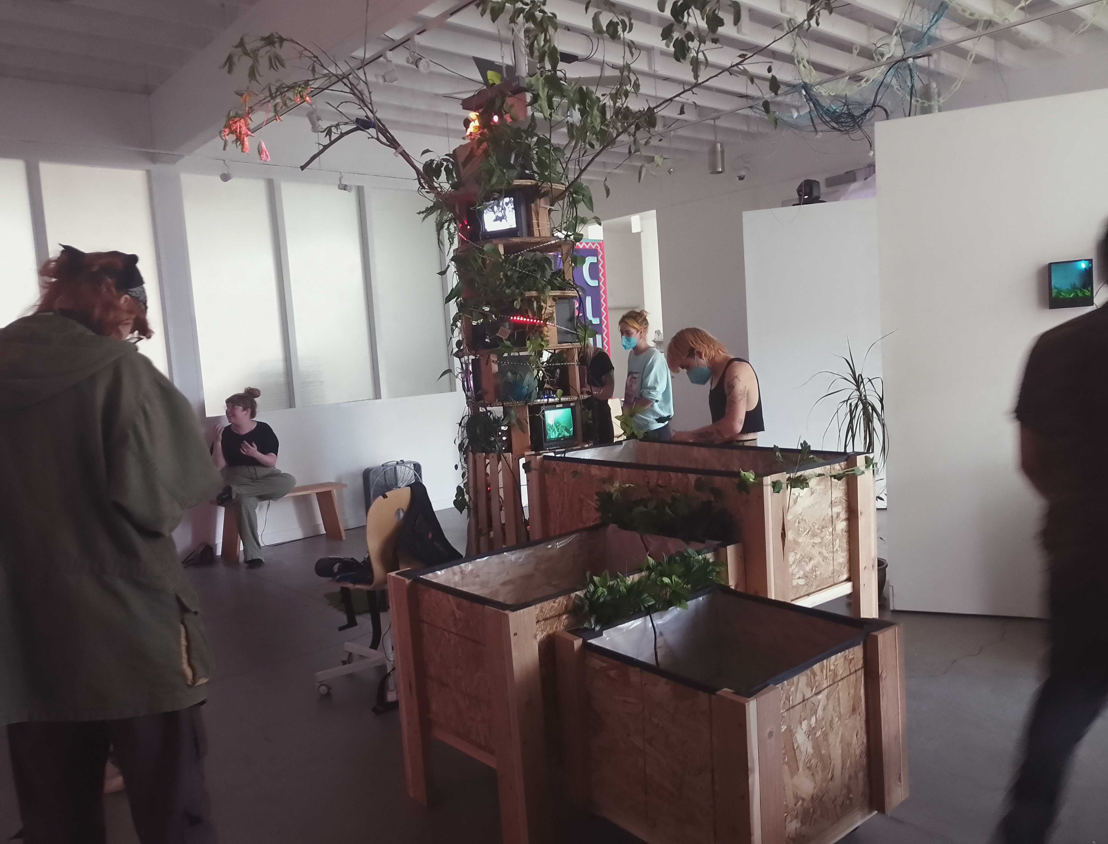
images/eventsNews/thethirdthing4.jpg
