DillonSimeone/ConfluenceTactoLuminateBracelet/images/eventsNews/thethirdthing5.jpg

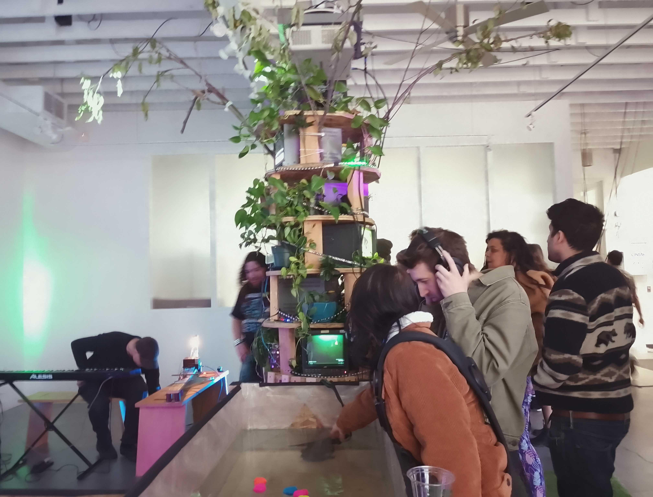
images/eventsNews/thethirdthing5.jpg
