DillonSimeone/ConfluenceTactoLuminateBracelet/images/eventsNews/thethirdthing.jpg

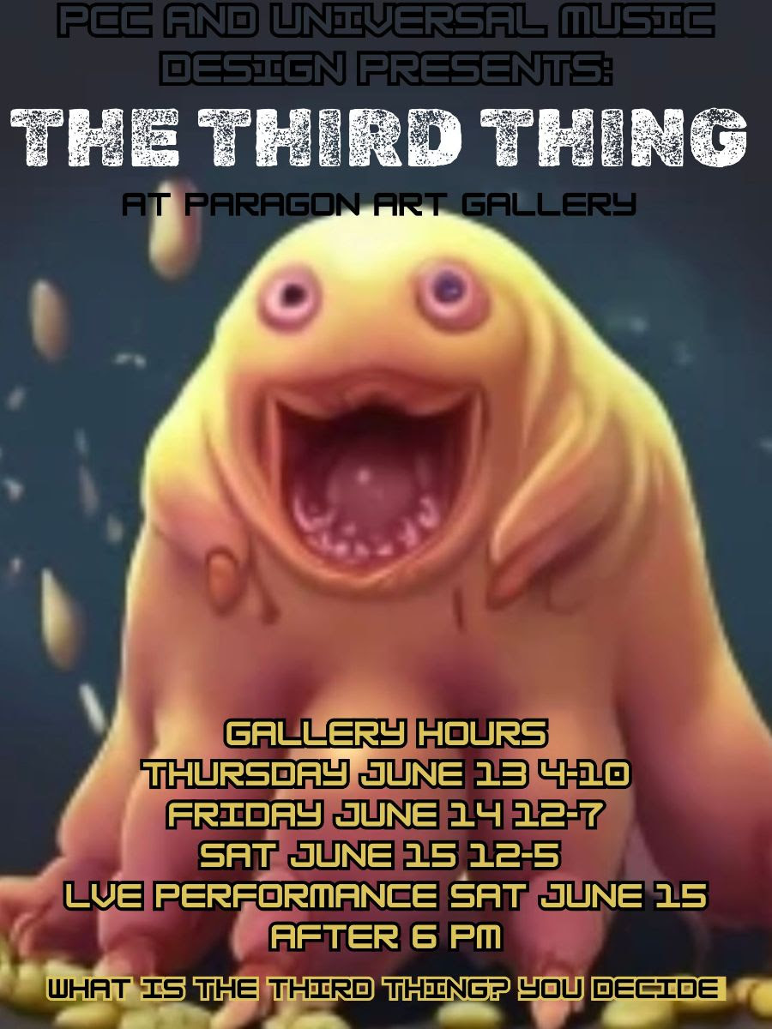
images/eventsNews/thethirdthing.jpg
