DillonSimeone/ConfluenceTactoLuminateBracelet/images/eventsNews/UnboxingDay.jpg

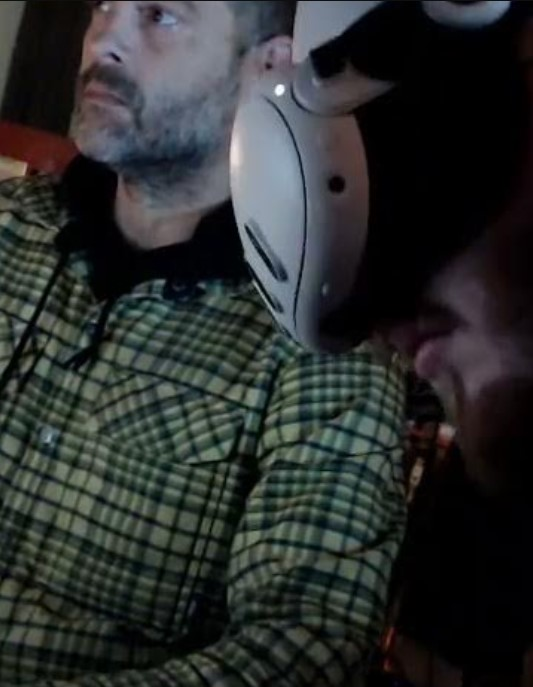
images/eventsNews/UnboxingDay.jpg
