DillonSimeone/ConfluenceTactoLuminateBracelet/images/Gestolumina/customPCBSchemes.jpg

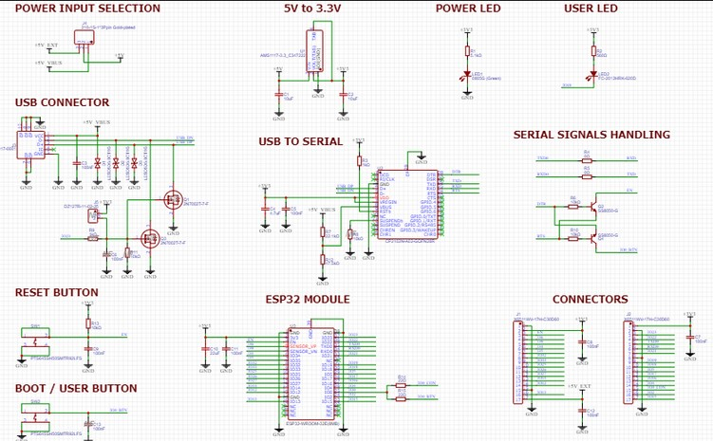
images/Gestolumina/customPCBSchemes.jpg
