DillonSimeone/ConfluenceTactoLuminateBracelet/images/Gestolumina/firstDeath2.jpg

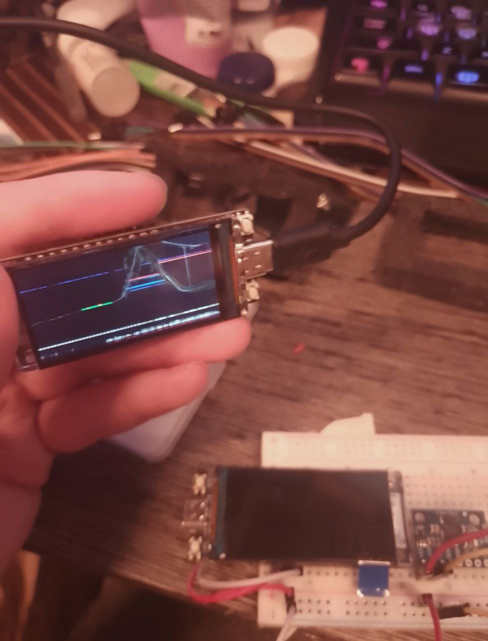
images/Gestolumina/firstDeath2.jpg
