DillonSimeone/ConfluenceTactoLuminateBracelet/images/Gestolumina/firstDeath.jpg

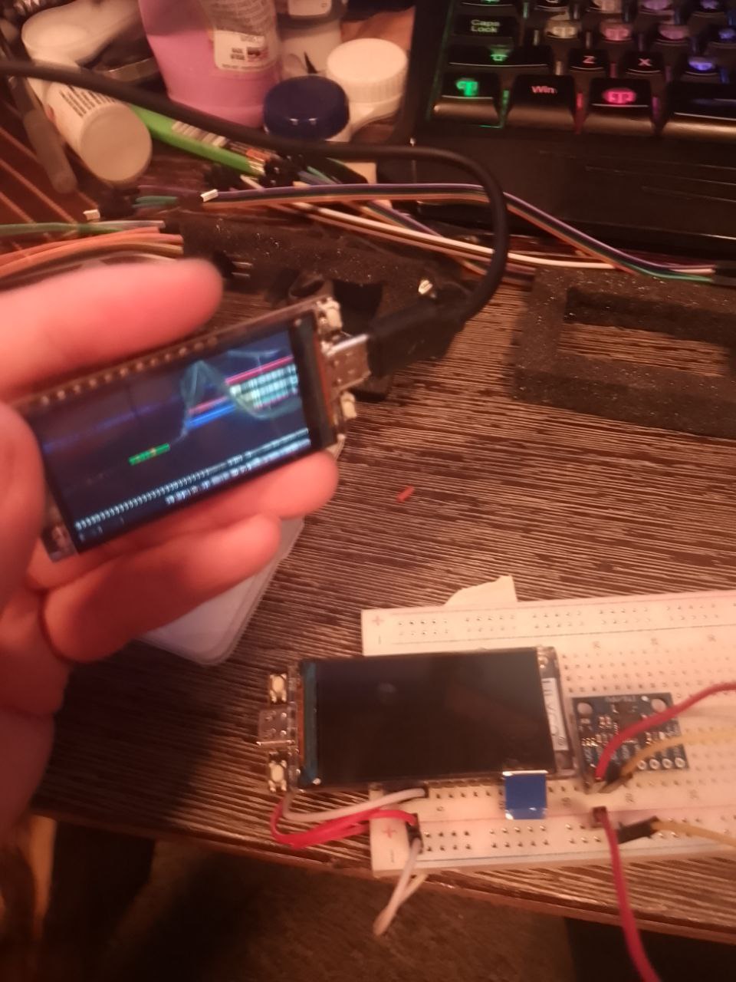
images/Gestolumina/firstDeath.jpg
