DillonSimeone/ConfluenceTactoLuminateBracelet/images/Gestolumina/idealGlove2.jpg

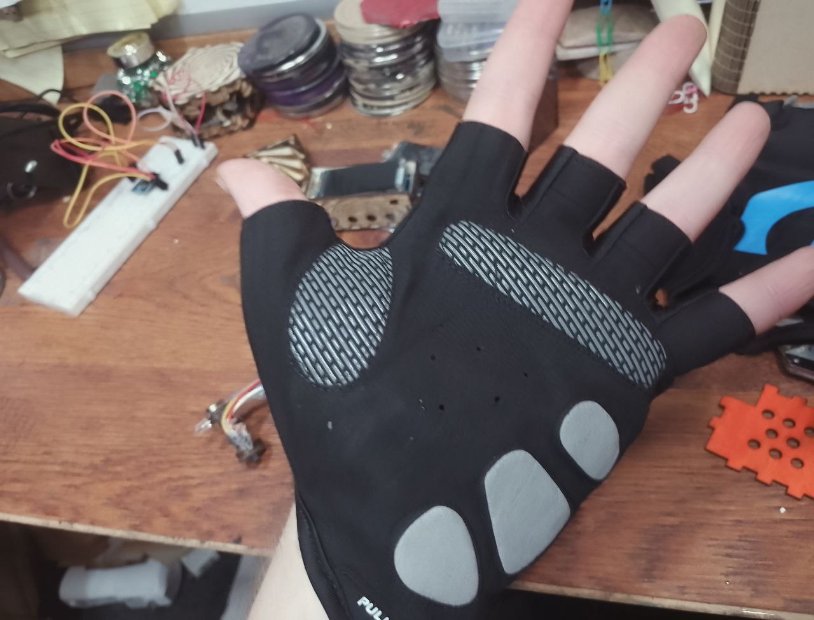
images/Gestolumina/idealGlove2.jpg
