DillonSimeone/ConfluenceTactoLuminateBracelet/images/Gestolumina/spidernest.jpg

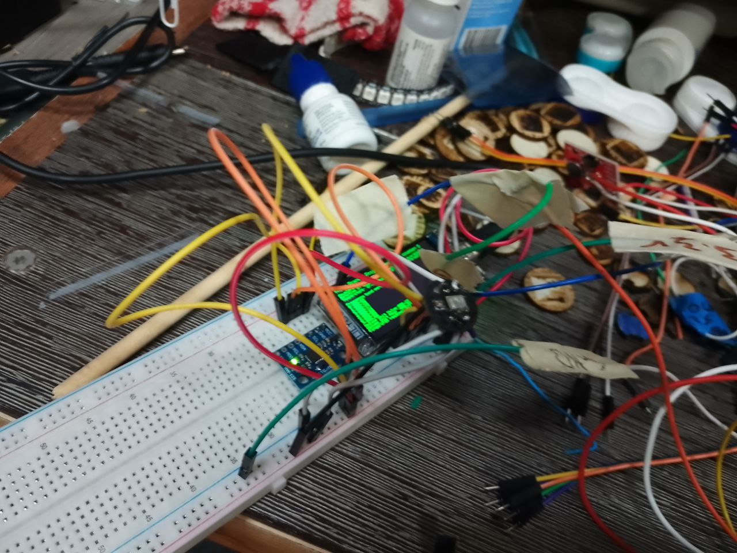
images/Gestolumina/spidernest.jpg
