DillonSimeone/ConfluenceTactoLuminateBracelet/images/placeHolder/news_1335912.png

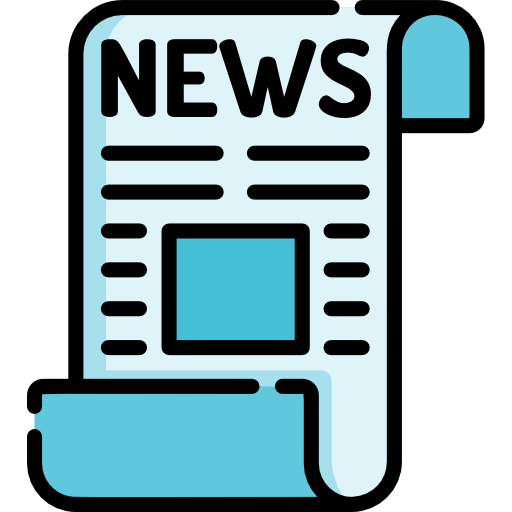
images/placeHolder/news_1335912.png
