DillonSimeone/ConfluenceTactoLuminateBracelet/images/subpac/Nate_subpac.png

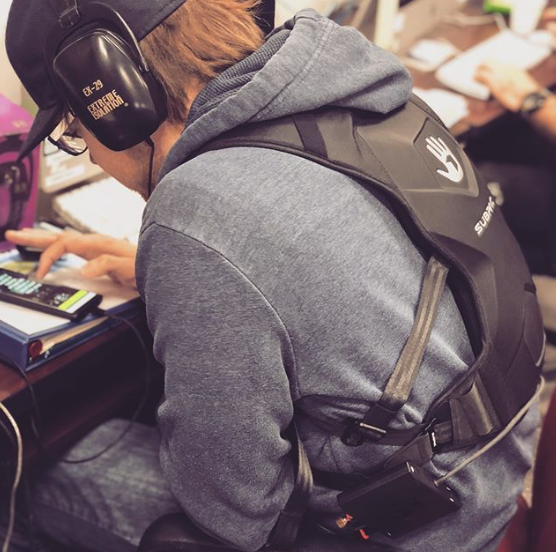
images/subpac/Nate_subpac.png
