DillonSimeone/ConfluenceTactoLuminateBracelet/images/SynchroGlove/D9OFSensor.jpg

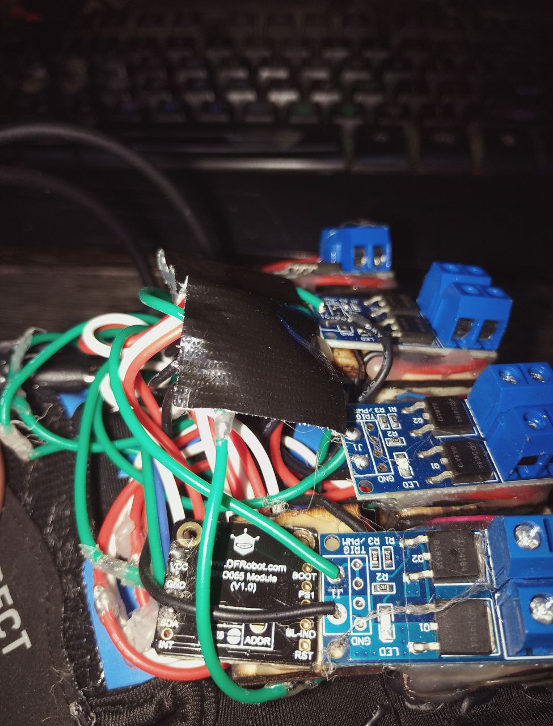
images/SynchroGlove/D9OFSensor.jpg
