DillonSimeone/ConfluenceTactoLuminateBracelet/images/SynchroGlove/DatGloves2.jpg

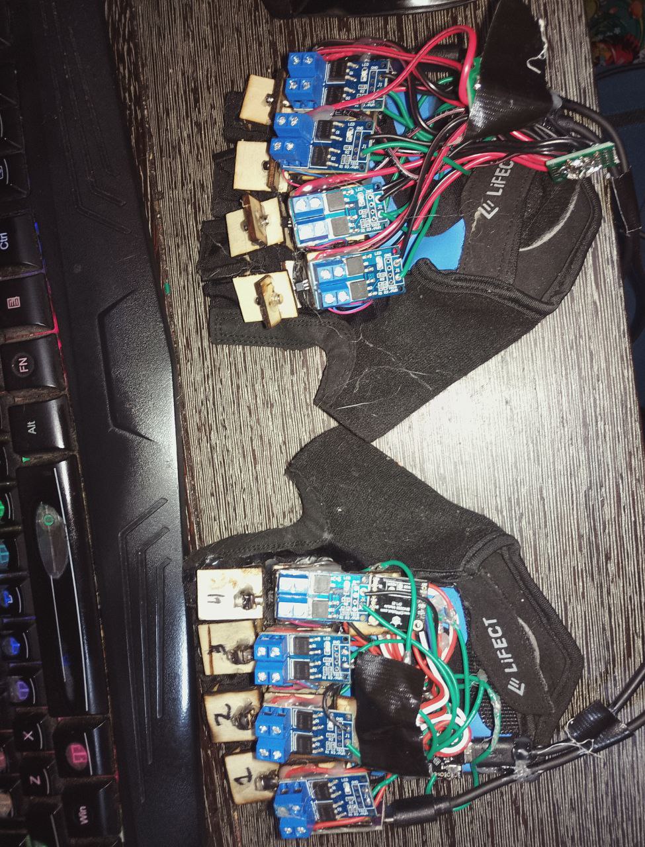
images/SynchroGlove/DatGloves2.jpg
