DillonSimeone/ConfluenceTactoLuminateBracelet/images/SynchroGlove/DatGloves3.jpg

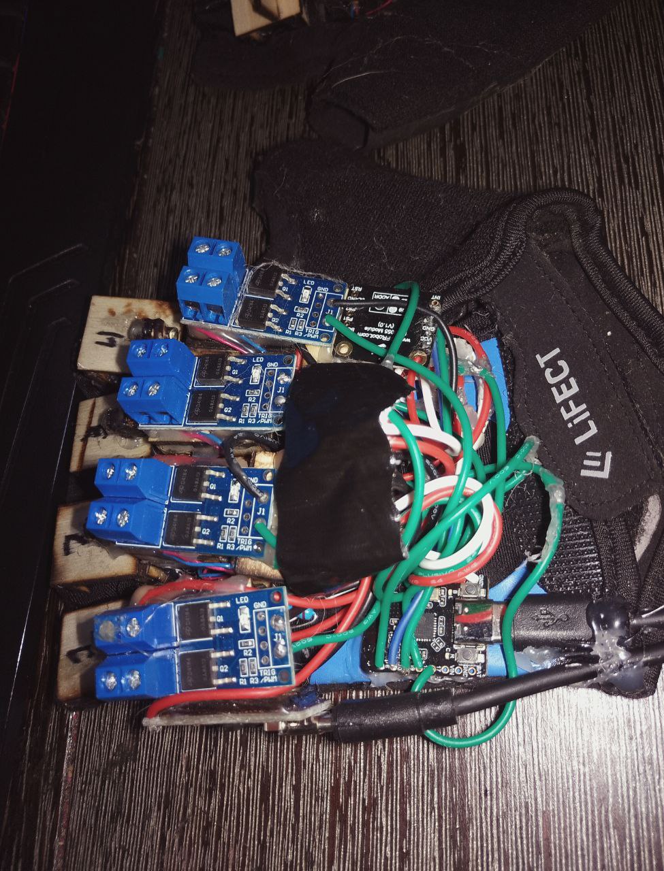
images/SynchroGlove/DatGloves3.jpg
