DillonSimeone/ConfluenceTactoLuminateBracelet/images/SynchroGlove/DatGloves4.jpg

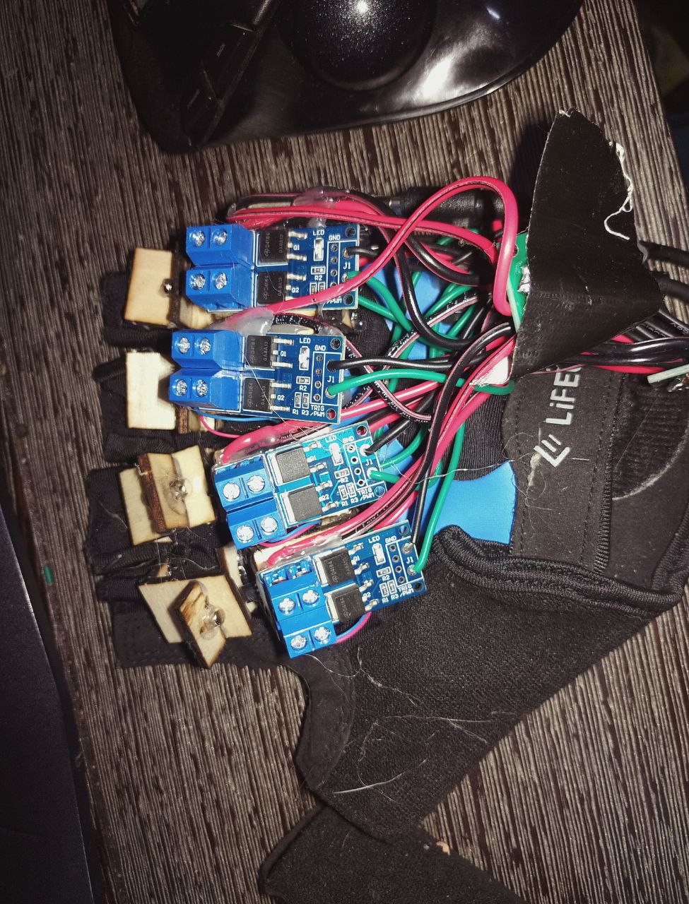
images/SynchroGlove/DatGloves4.jpg
