DillonSimeone/ConfluenceTactoLuminateBracelet/images/SynchroGlove/DatGloves.jpg

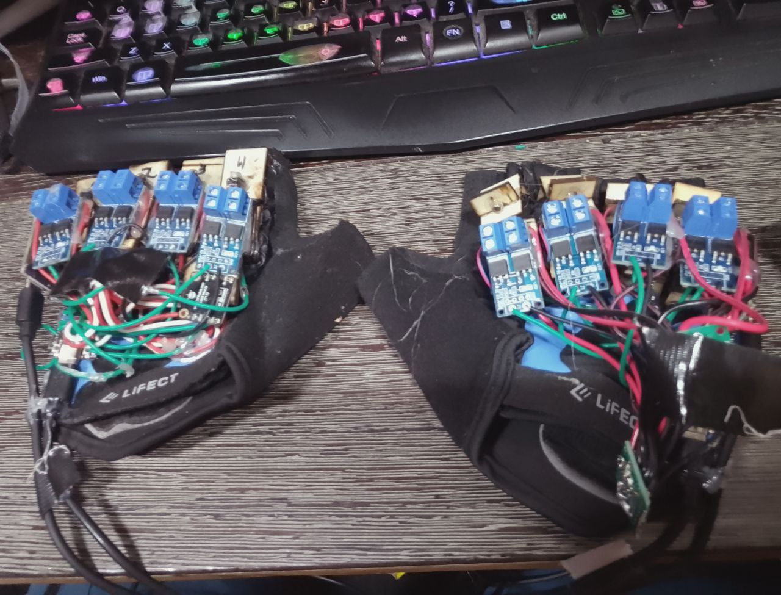
images/SynchroGlove/DatGloves.jpg
