DillonSimeone/ConfluenceTactoLuminateBracelet/images/SynchroGlove/HallwaySensorMagnetsMotors.jpg

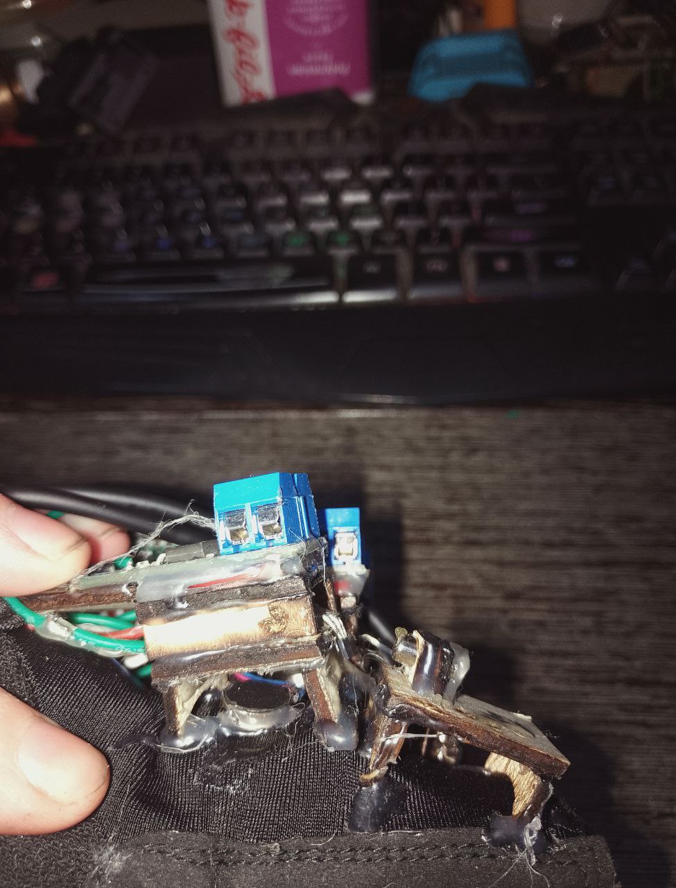
images/SynchroGlove/HallwaySensorMagnetsMotors.jpg
