DillonSimeone/ConfluenceTactoLuminateBracelet/images/SynchroGlove/praiseShrek.jpg

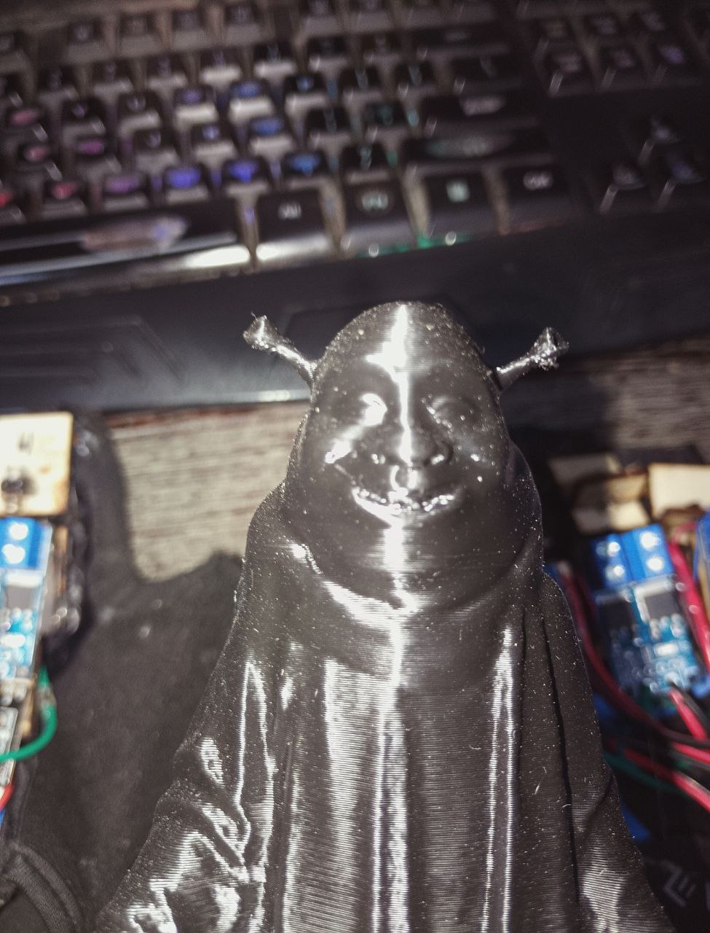
images/SynchroGlove/praiseShrek.jpg
