DillonSimeone/ConfluenceTactoLuminateBracelet/images/teamMembers/FOUNDERS.jpeg

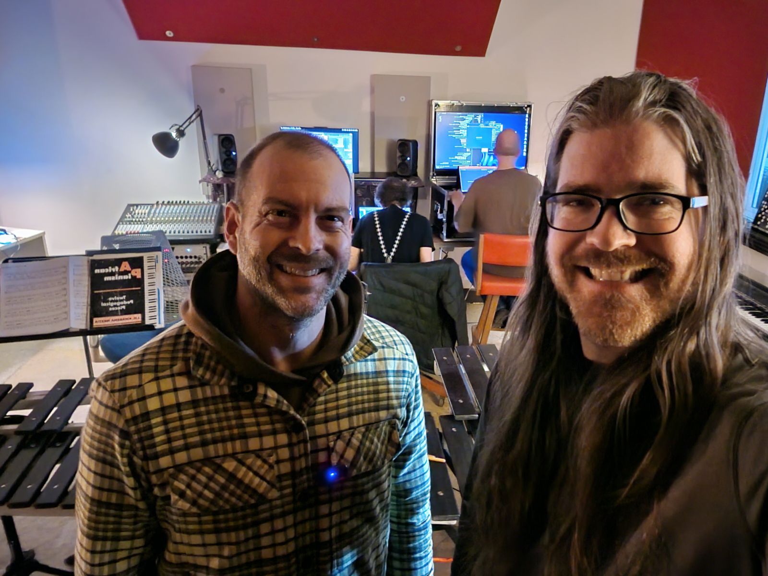
images/teamMembers/FOUNDERS.jpeg
