DillonSimeone/ConfluenceTactoLuminateBracelet/images/teamMembers/nateHegent.jpg

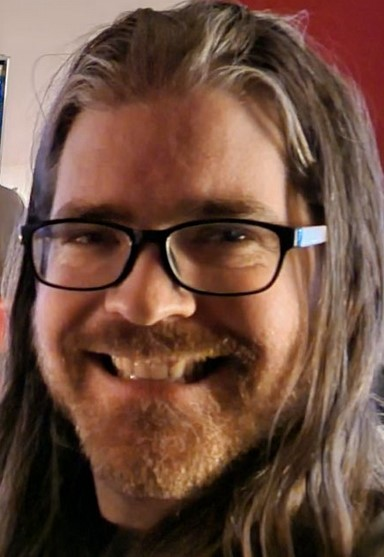
images/teamMembers/nateHegent.jpg
