DillonSimeone/ConfluenceTactoLuminateBracelet/images/teamMembers/shawnTrail.jpg

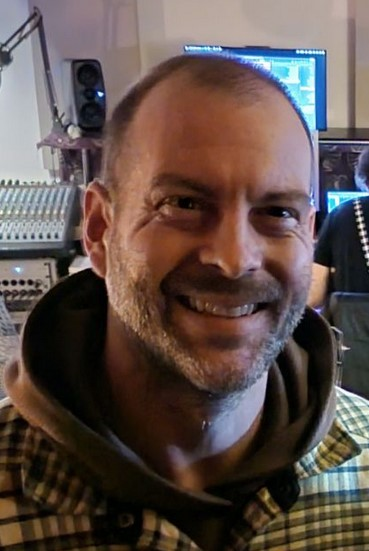
images/teamMembers/shawnTrail.jpg
