DillonSimeone/ConfluenceTactoLuminateBracelet/images/teamMembers/teamMembers.jpg

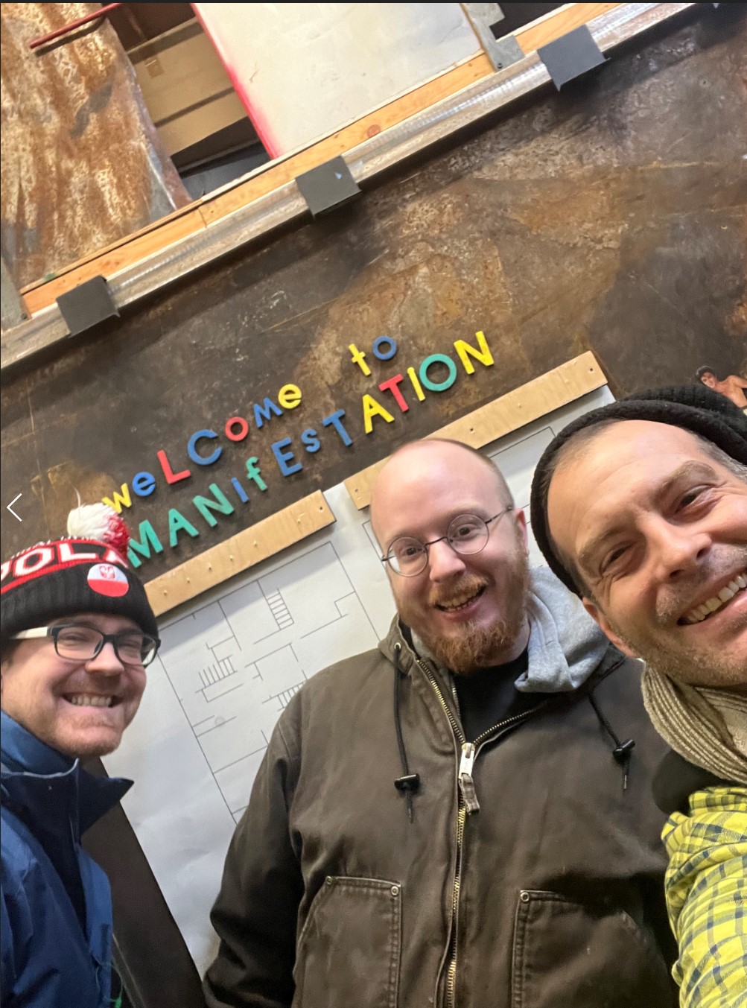
images/teamMembers/teamMembers.jpg
