DillonSimeone/ConfluenceTactoLuminateBracelet/images/UniversalMusicDesignAffilateMarketing.png

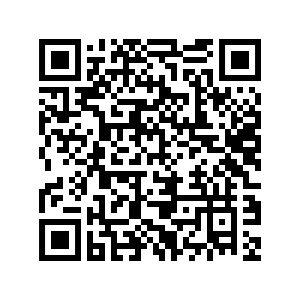
images/UniversalMusicDesignAffilateMarketing.png
