DillonSimeone/ConfluenceTactoLuminateBracelet/images/WebsiteMetrics/2024_4_30.jpg

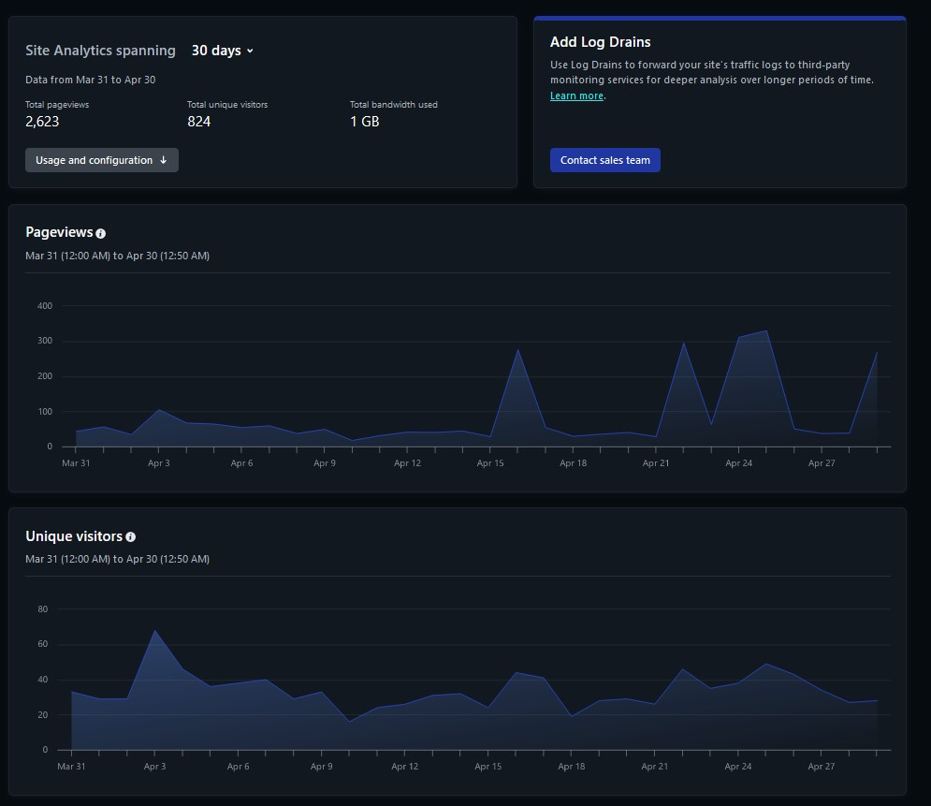
images/WebsiteMetrics/2024_4_30.jpg
