DillonSimeone/ConfluenceTactoLuminateBracelet/images/WebsiteMetrics/Feb10ToMarch12.png

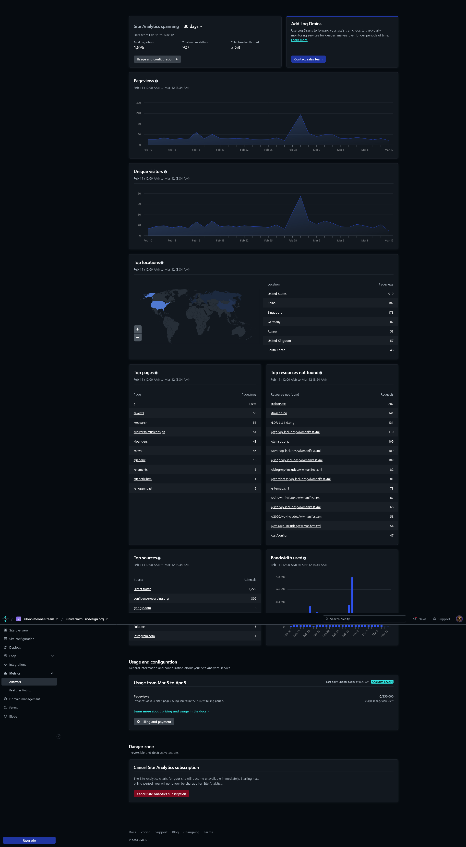
images/WebsiteMetrics/Feb10ToMarch12.png
