DillonSimeone/ConfluenceTactoLuminateBracelet/images/WebsiteMetrics/Page5_6_2024.png

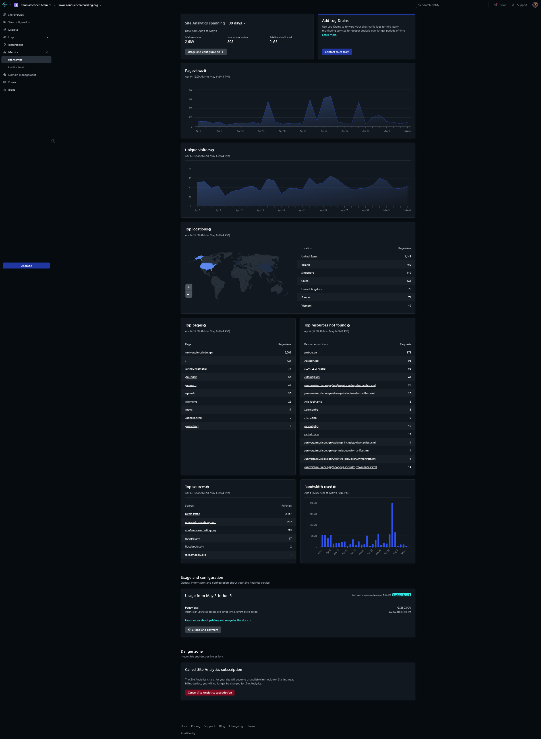
images/WebsiteMetrics/Page5_6_2024.png
