DillonSimeone/ConfluenceTactoLuminateBracelet/images/WebsiteMetrics/TopPages.jpg

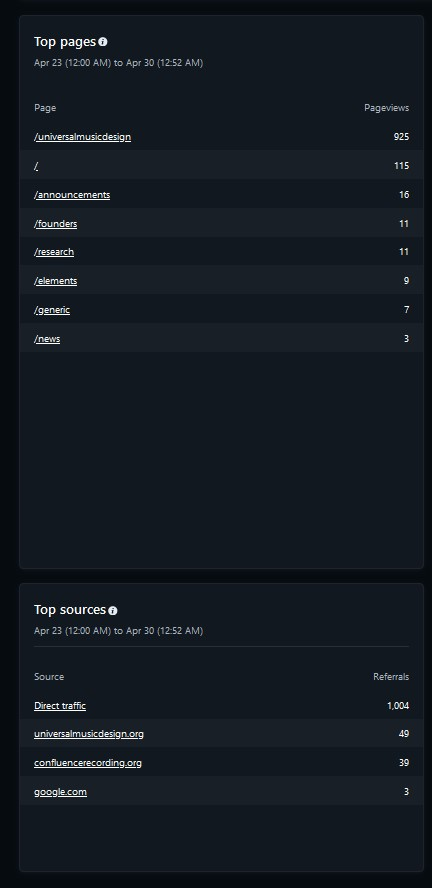
images/WebsiteMetrics/TopPages.jpg
