DillonSimeone/ConfluenceTactoLuminateBracelet/images/Gestolumina/wiringFun.jpg

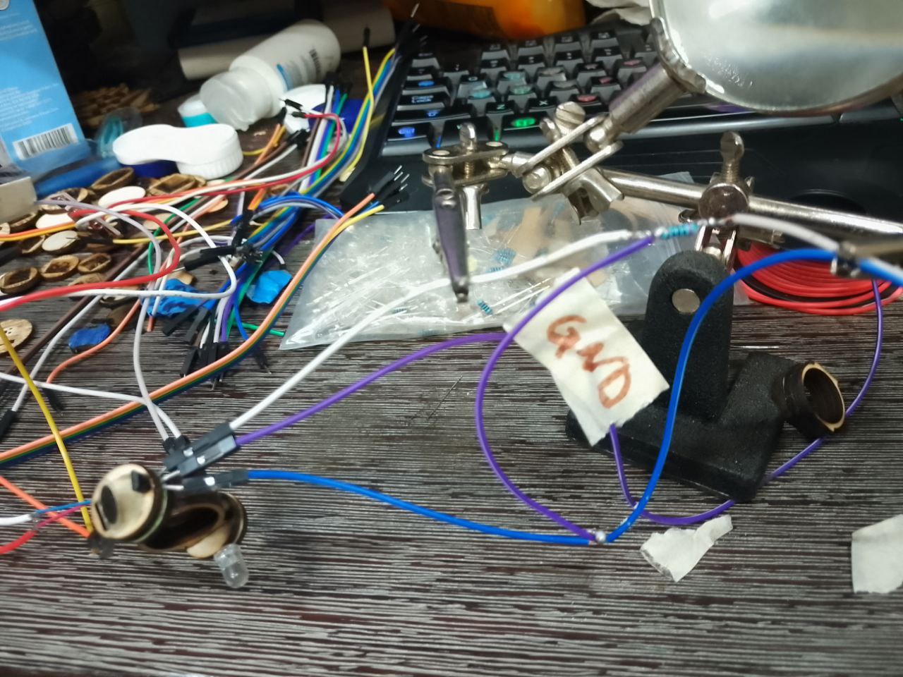
images/Gestolumina/wiringFun.jpg
