DillonSimeone/ConfluenceTactoLuminateBracelet/images/Gestolumina/Testing Haptics.jpg

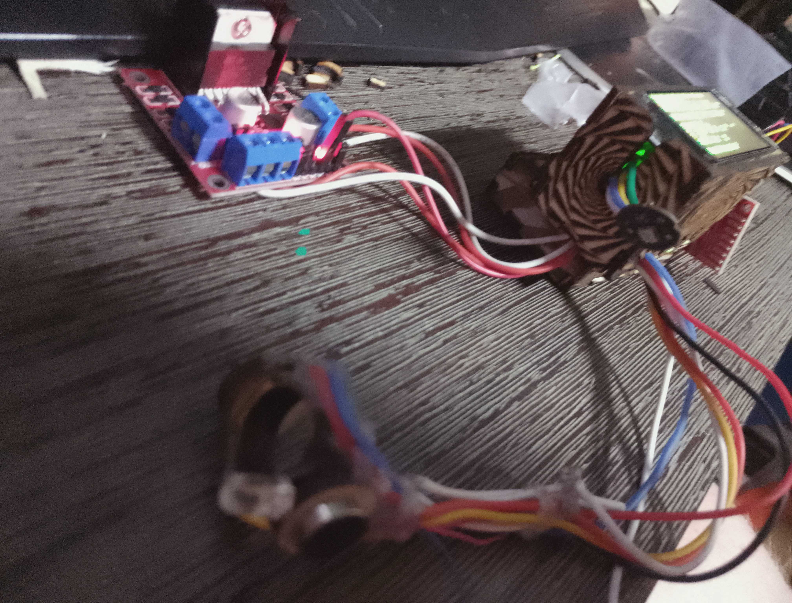
images/Gestolumina/Testing Haptics.jpg
