DillonSimeone/ConfluenceTactoLuminateBracelet/images/Gestolumina/testingBox2.jpg

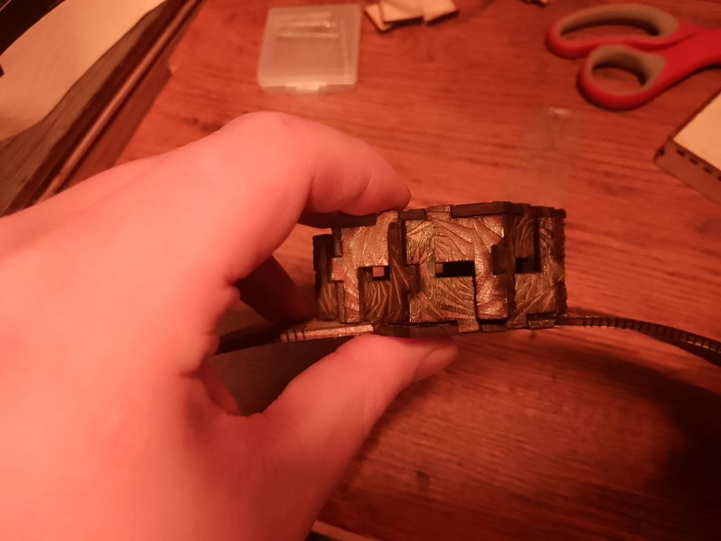
images/Gestolumina/testingBox2.jpg
