DillonSimeone/ConfluenceTactoLuminateBracelet/images/Gestolumina/testingBoxFit2.jpg

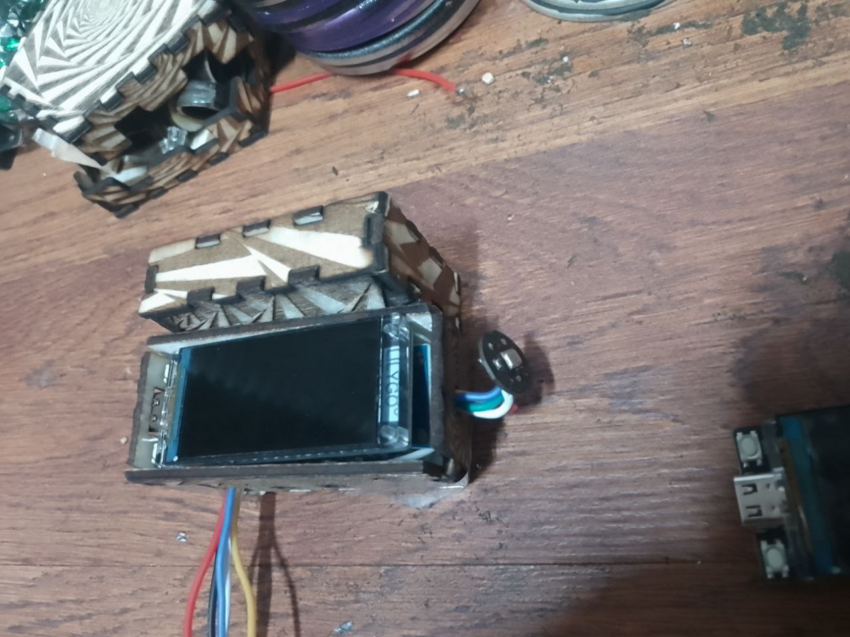
images/Gestolumina/testingBoxFit2.jpg
