DillonSimeone/ConfluenceTactoLuminateBracelet/images/Gestolumina/testingBoxFit3.jpg

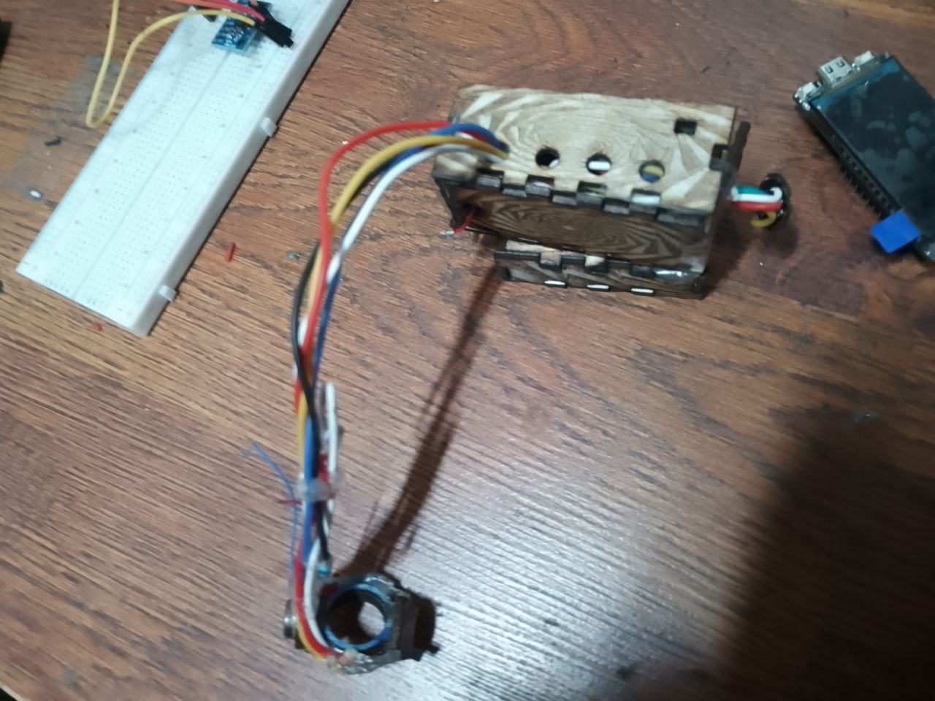
images/Gestolumina/testingBoxFit3.jpg
