DillonSimeone/ConfluenceTactoLuminateBracelet/images/Gestolumina/testingESP32Display2.png

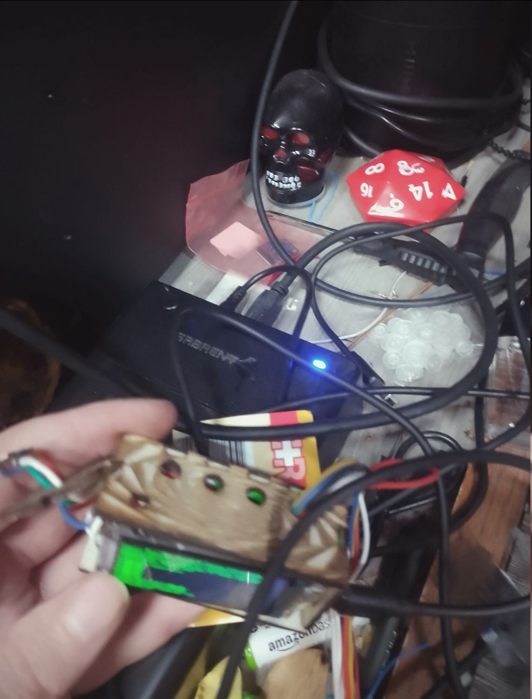
images/Gestolumina/testingESP32Display2.png
