DillonSimeone/ConfluenceTactoLuminateBracelet/images/Gestolumina/testingFit2.jpg

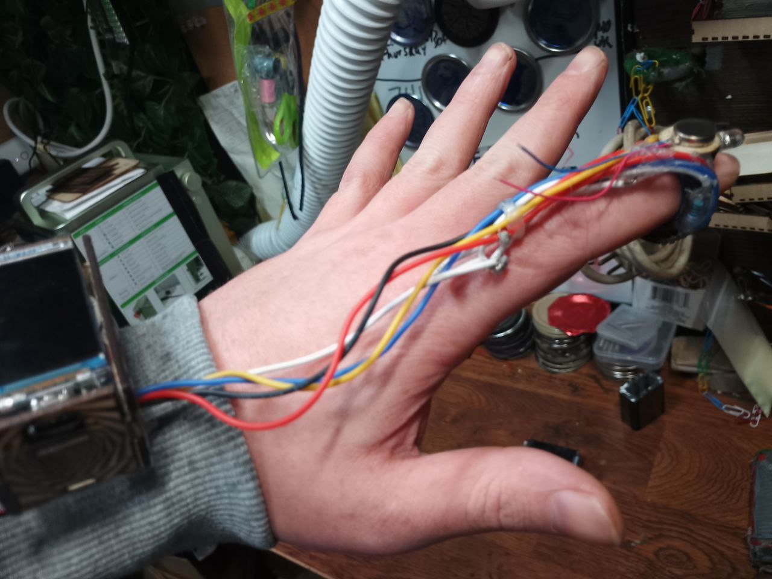
images/Gestolumina/testingFit2.jpg
