DillonSimeone/ConfluenceTactoLuminateBracelet/images/Gestolumina/testingMagicRing1.jpg

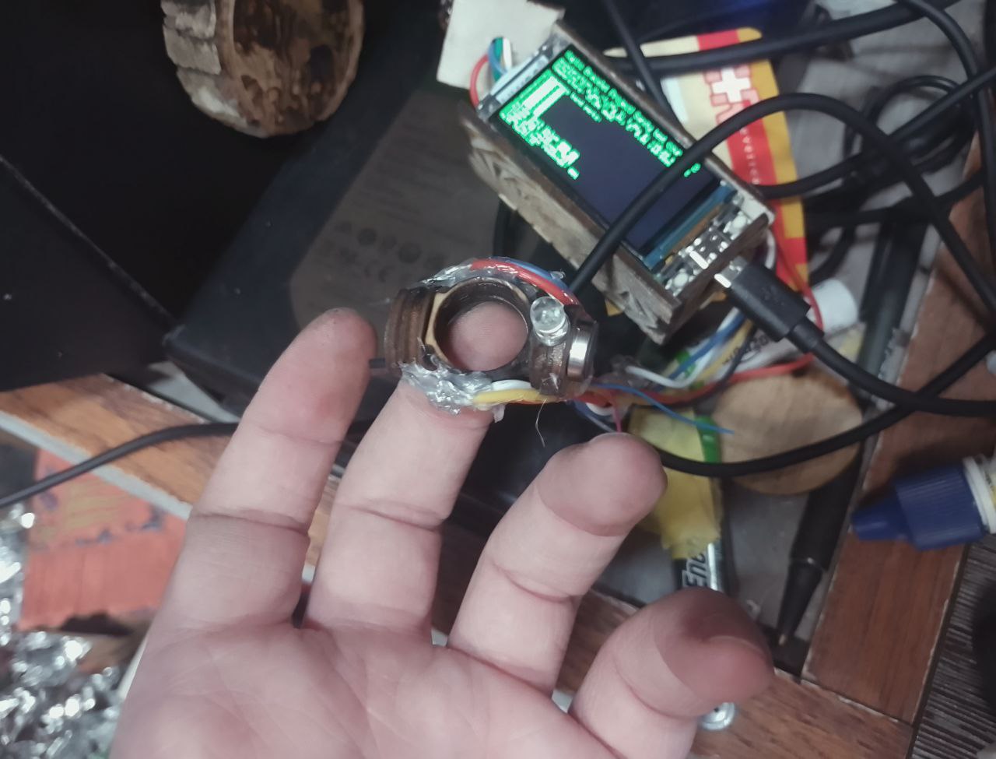
images/Gestolumina/testingMagicRing1.jpg
