DillonSimeone/ConfluenceTactoLuminateBracelet/images/Gestolumina/testingMic2.jpg

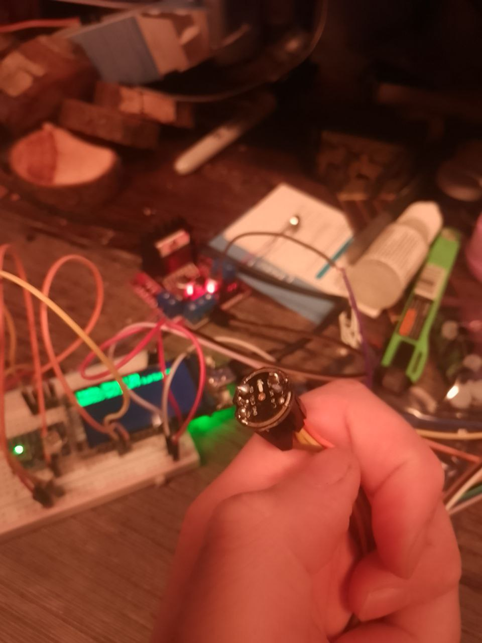
images/Gestolumina/testingMic2.jpg
